abaffa/zx81/case_zx80/vacuum_mold2/48836-sinclair-zx80-vacuum-form-molds-40aaf106-83d1-470b-8c4a-8a237495e2ef.pdf

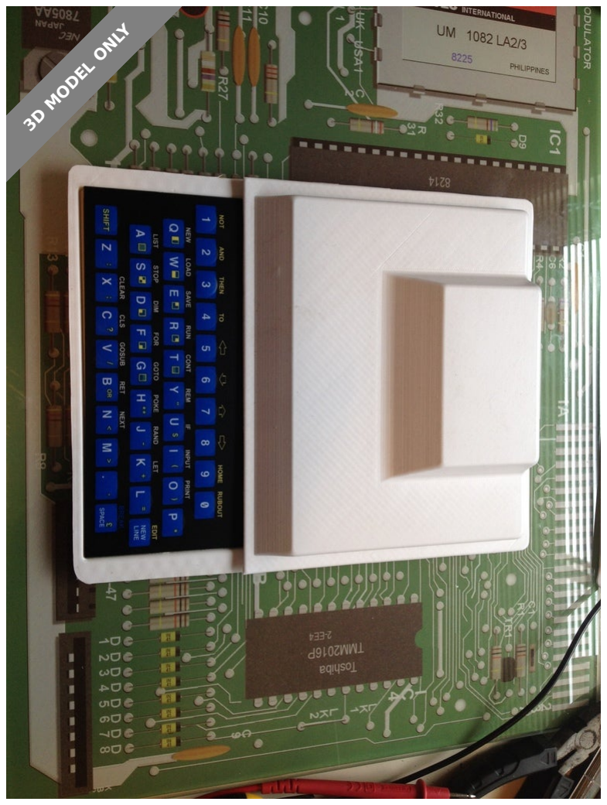
[picture p41: figure]
3D MODEL ONLY

## Summary

This is a first attempt at a vacuum form mold set for the Sinclair ZX80 computer. The ZX80's case was originally vacuum formed from polystyrene sheets, only later becoming injection molded.

This is an attempt to produce simple molds that can be made to replace the original cases which have become very brittle due to their age, or for a new ZX80 replica. The Sinclair ZX80 computer was produced by a company called "Science Of Cambridge" (Later renamed Sinclar Research) in 1980 and was powered by the Zilog Z80 Microprocessor and utilized 4k of Rom and 1k of Ram.

Hobby & Makers (https://www.prusaprinters.org/prints?categoryId=48) > Electronics (https://www.prusaprinters.org/prints?categoryId=52)

zx80 | sinclair | case

w (https://www.prusaprinters.org/social/27897/prints) wjsteele (https://www.prusaprinters.org/social/27897/prints)

## Sinclair ZX80 Vacuum Form Molds

VIEW IN BROWSER (https://www.prusaprinters.org/prints/48836-sinclair-zx80-vacuum-form-molds)

updated 14. 12. 2020 | published 14. 12. 2020

Model Files (.stl, .3mf, .obj, .amf) | F3 3D DOWNLOAD ALL FILES (https://www.prusaprinters.org/prints/48836-sinclair-zx80-vacuum-form-molds/files)

18.1 KB
updated 14. 12. 2020

F3
3D (https://www.prusaprinters.org/prints/48836-sinclair-zx80-vacuum-form-molds/files)

59.3 KB
updated 14. 12. 2020

F3
3D (https://www.prusaprinters.org/prints/48836-sinclair-zx80-vacuum-form-molds/files)

2.6 MB
updated 14. 12. 2020

F3
3D (https://www.prusaprinters.org/prints/48836-sinclair-zx80-vacuum-form-molds/files)

6.0 MB
updated 14. 12. 2020

F3
3D (https://www.prusaprinters.org/prints/48836-sinclair-zx80-vacuum-form-molds/files)

F3
0F

## Category: Computer Summary

This is a first attempt at a vacuum form mold set for the Sinclair ZX80 computer. The ZX80's case was originally vacuum formed from polystyrene sheets, only later becoming injection molded.

This is an attempt to produce simple molds that can be made to replace the original cases which have become very brittle due to their age, or for a new ZX80 replica. The Sinclair ZX80 computer was produced by a company called "Science Of Cambridge" (Later renamed Sinclar Research) in 1980 and was powered by the Zilog Z80 Microprocessor and utilized 4k of Rom and 1k of Ram.

Find source .stl files on Thingiverse.com (https://www.thingiverse.com/thing:2587664)

The Author has not uploaded any print files.
Try to search in User print files (https://www.prusaprinters.org/prints/48836-sinclair-zx80-vacuum-form-molds/user-gcodes) section or generate and upload your own.

zx80_top_mold.stl

zx80_top_mold.skp

zx80_bottom_mold.skp

zx80_bottom_mold.stl

## License

This work is licensed under a
Creative Commons (International License)

Public Domain (https://creativecommons.org/share-your-work/public-domain/cc0/)

✔ | Sharing without ATTRIBUTION
✔ | Remix Culture allowed
✔ | Commercial Use
✔ | Free Cultural Works
✔ | Meets Open Definition
