abaffa/zx81/keyboard/keyboard_acetate_separator.pdf

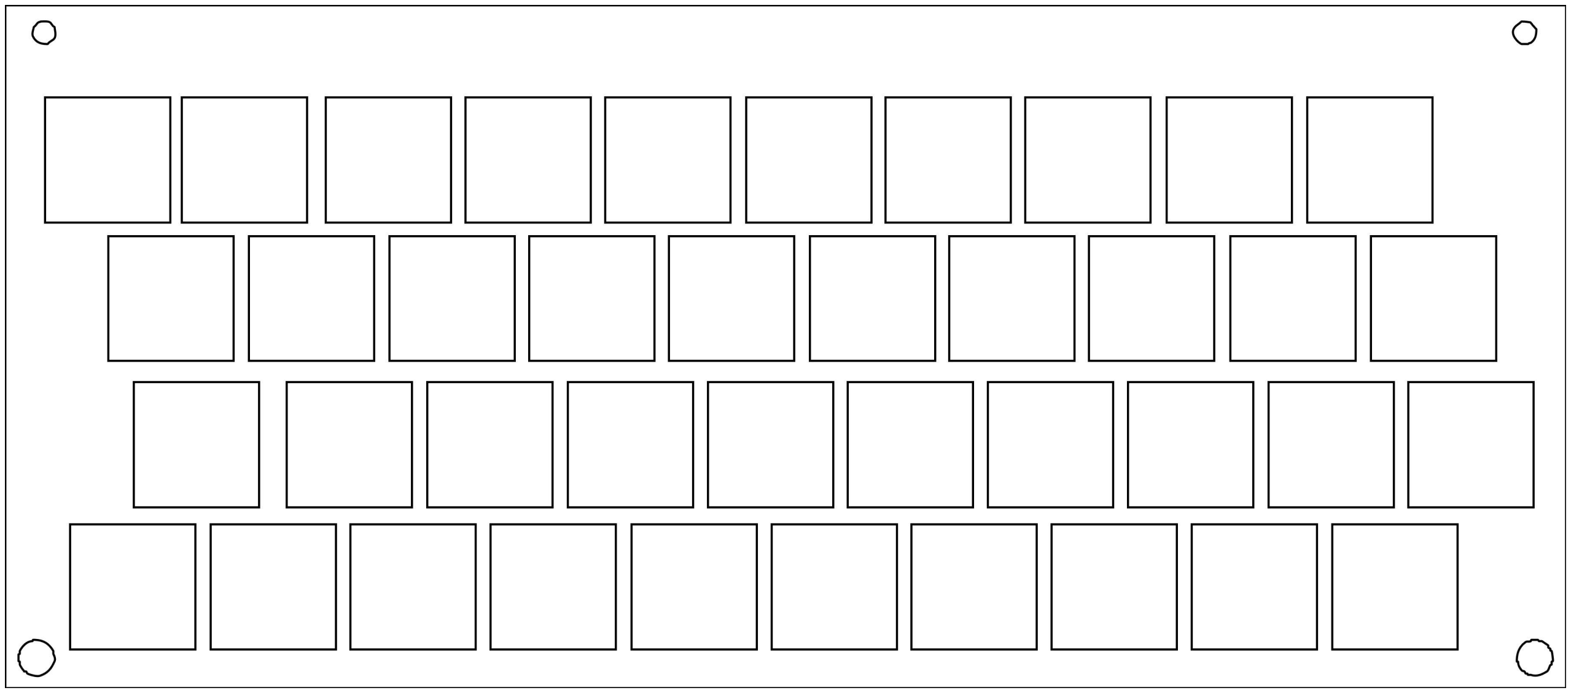
[picture p43: figure]
