abaffa/zx81/keyboard/keyboard_mask.pdf

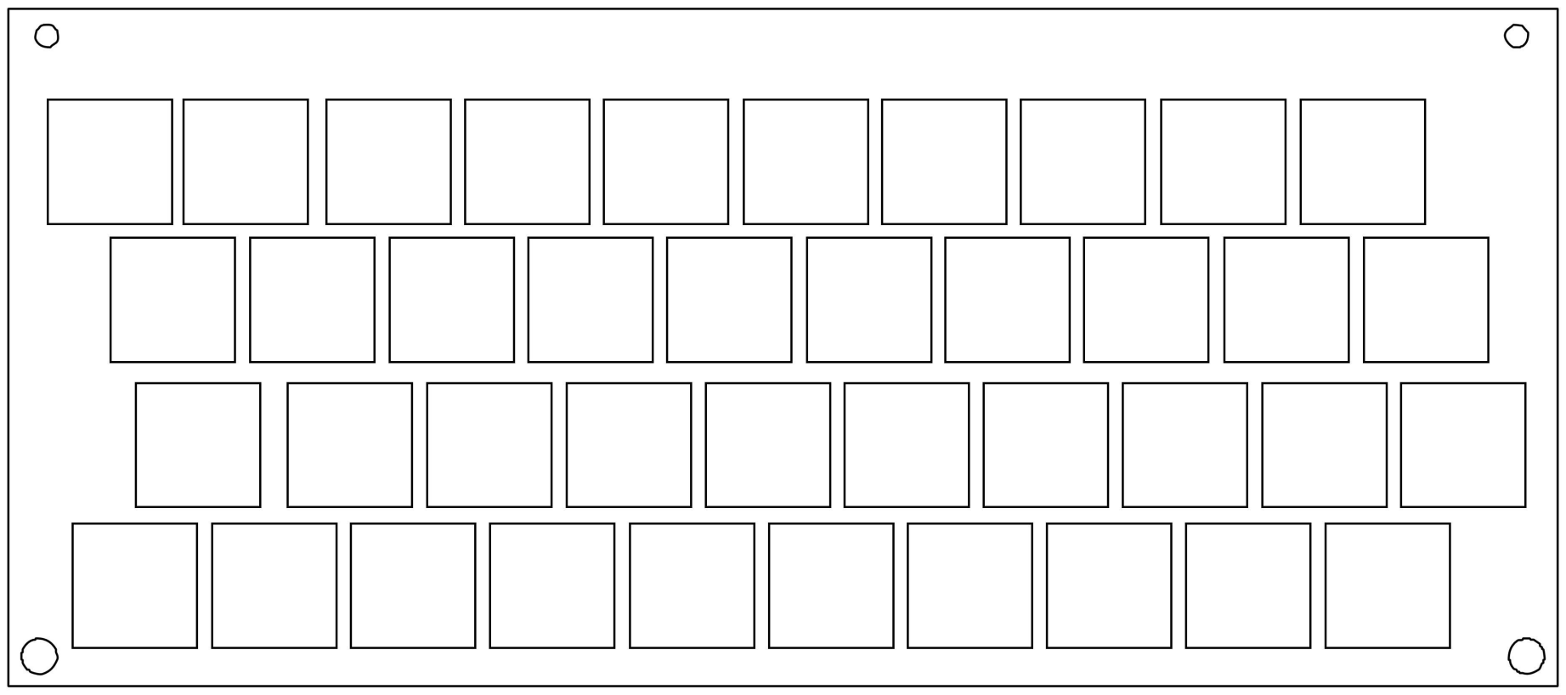
[picture p44: figure]
