abaffa/zx81/keyboard/keyboard_zx80_color.pdf

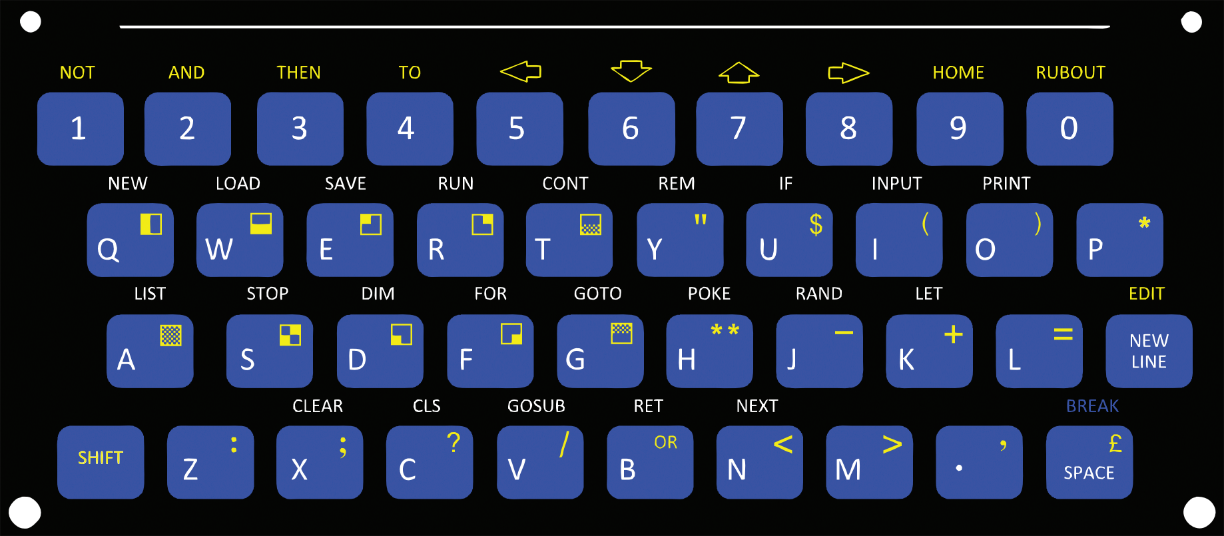
[picture p45: page 1]
