abaffa/zx81/keyboard/keyboard_zx80_pb_A4.pdf

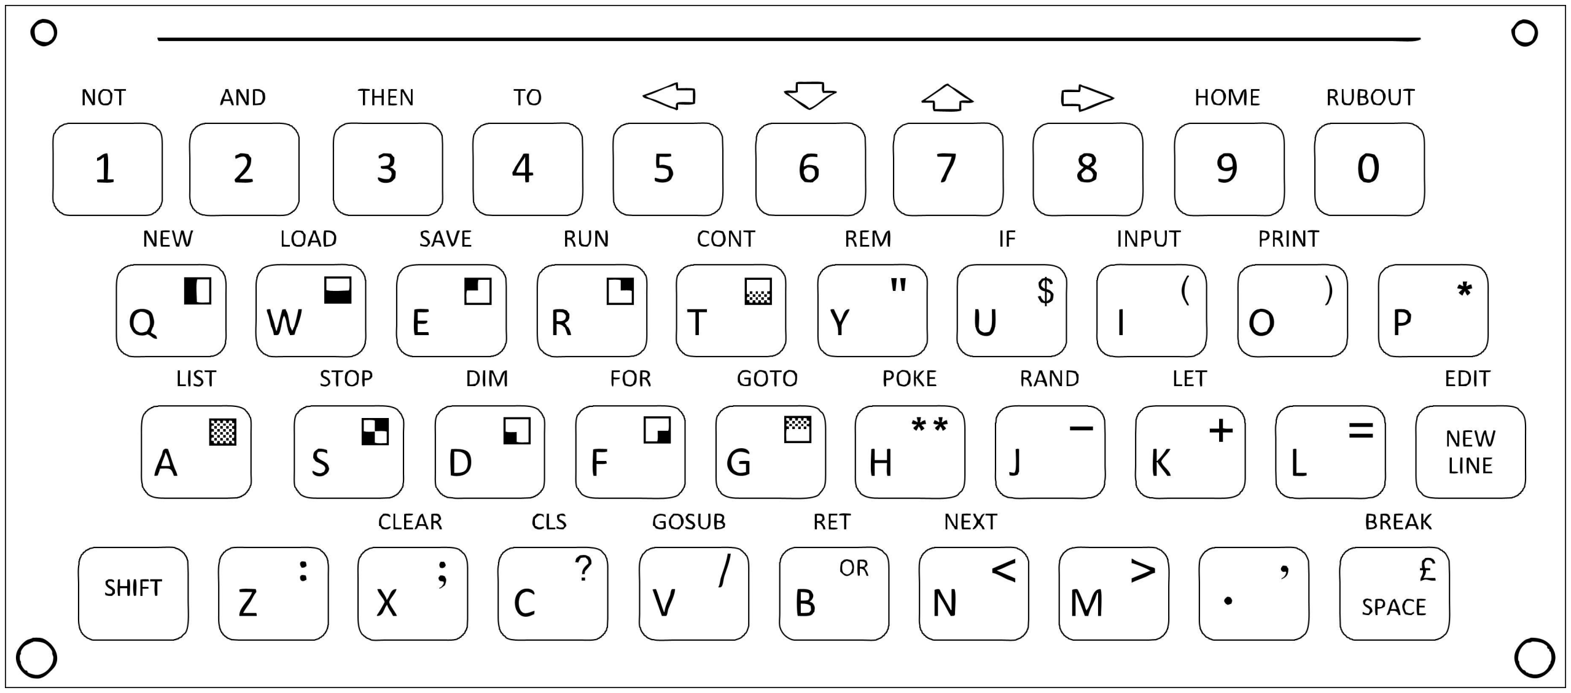
[picture p46: figure]
