abaffa/zx81/keyboard/keyboard_zx81_pb_A4.pdf

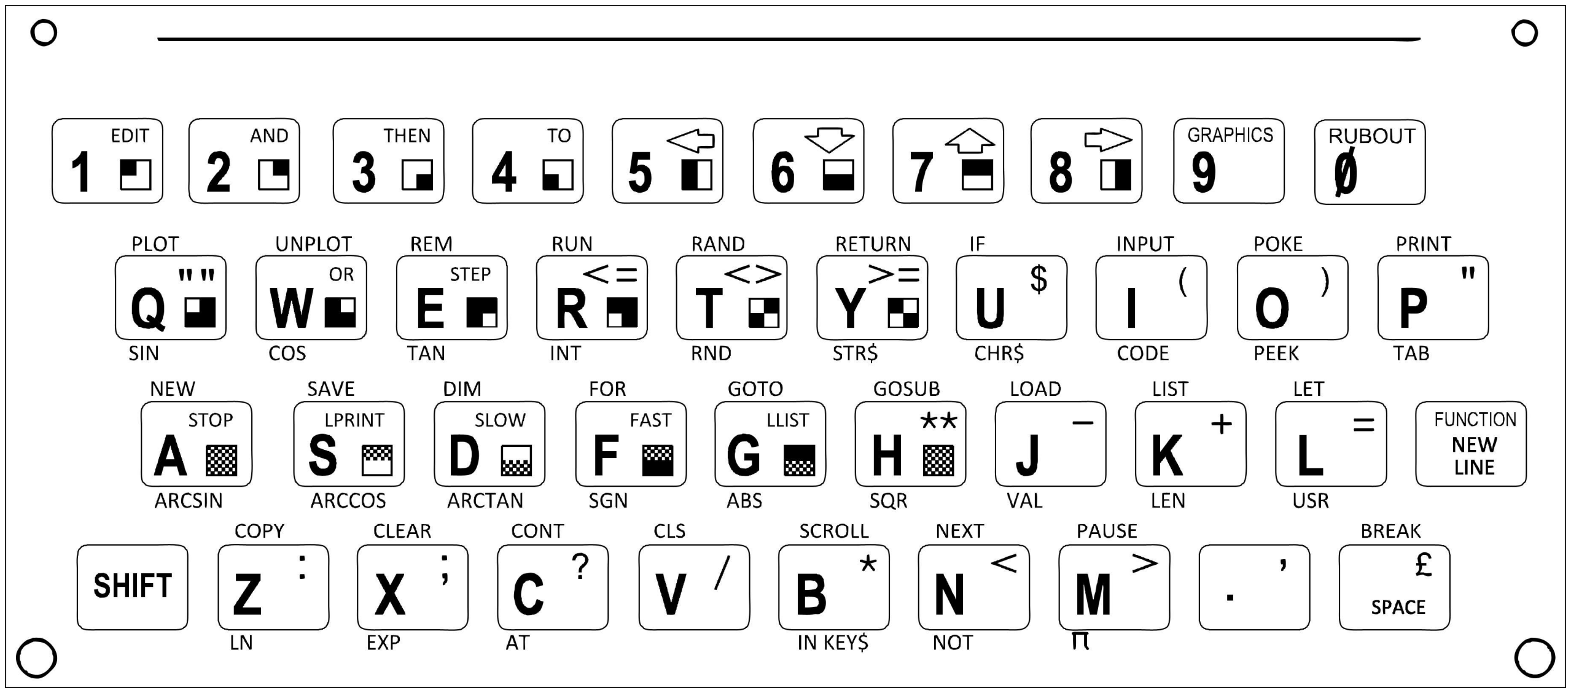
[picture p47: figure]
