abaffa/zx81/stickers/_sample_applied_stickers.pdf

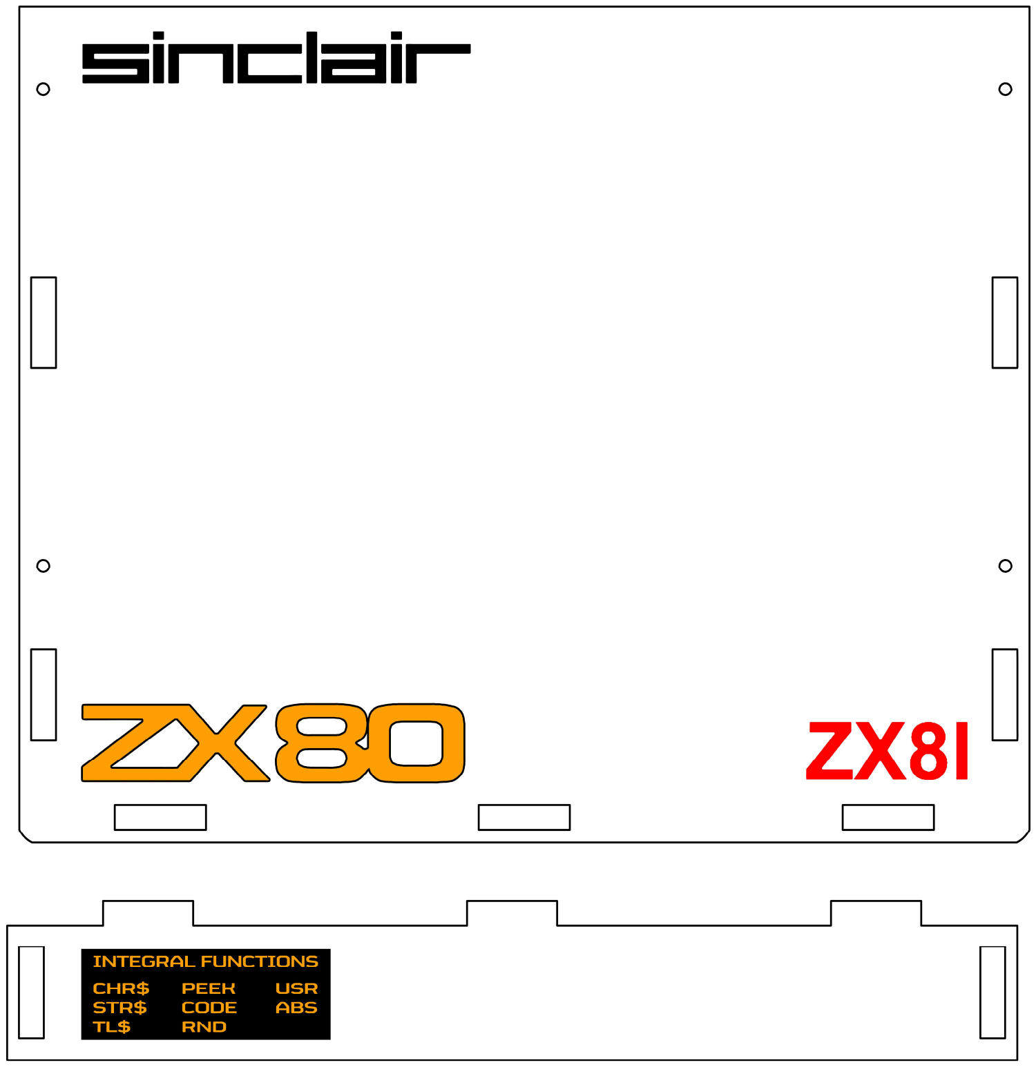
[picture p48: page 1]
