abaffa/zx81/stickers/Labels_ZX80.pdf

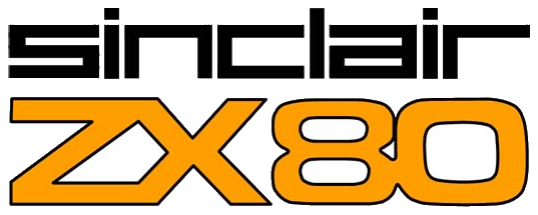
[picture p49: figure]
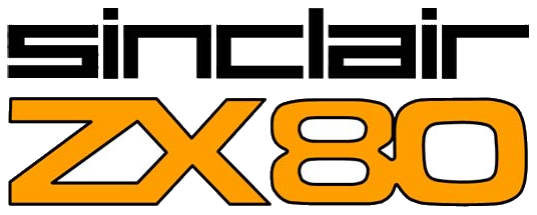
[picture p50: figure]
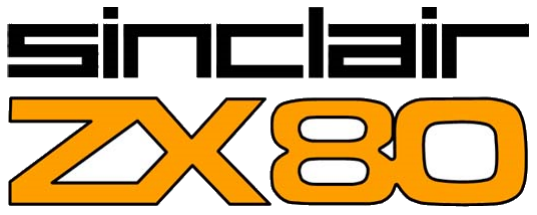
[picture p51: figure]
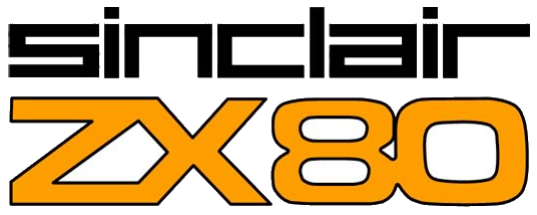
[picture p52: figure]
