abaffa/zx81/stickers/sticker_functions.pdf

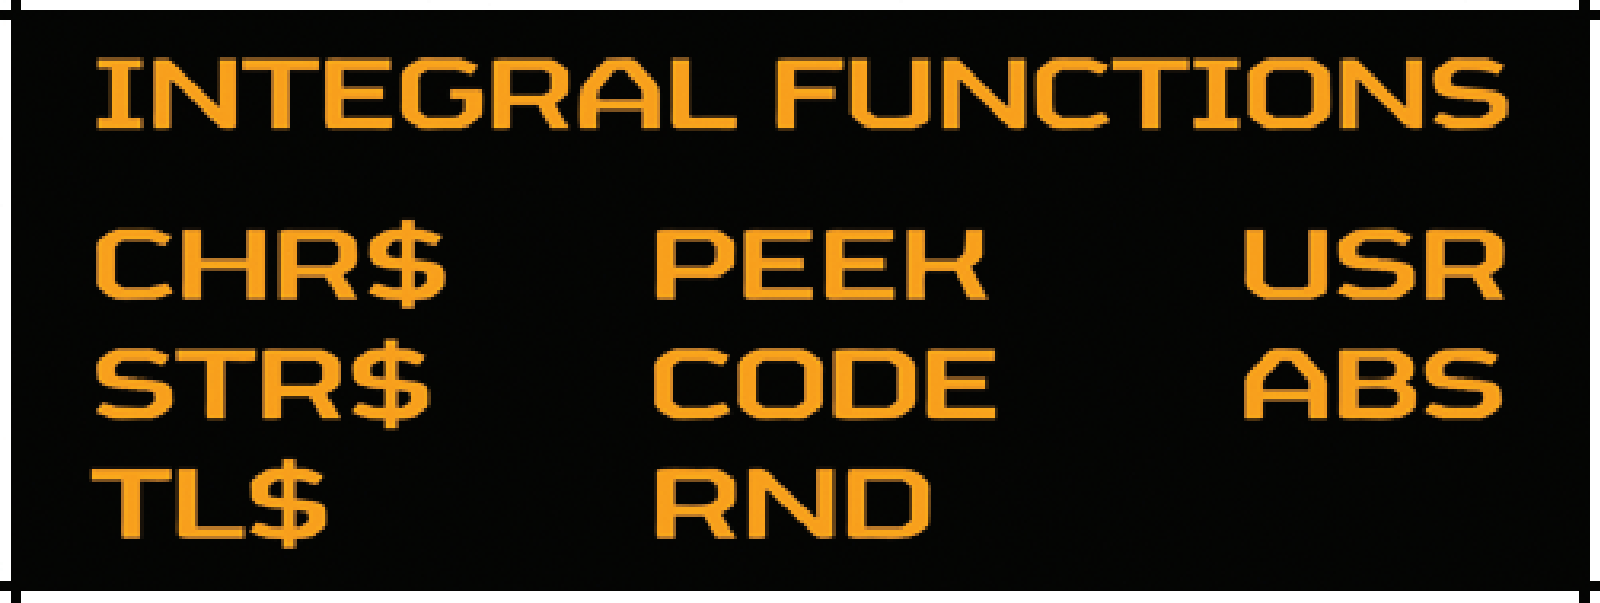
[picture p53: page 1]
