abaffa/zx81/stickers/sticker_zx80.pdf

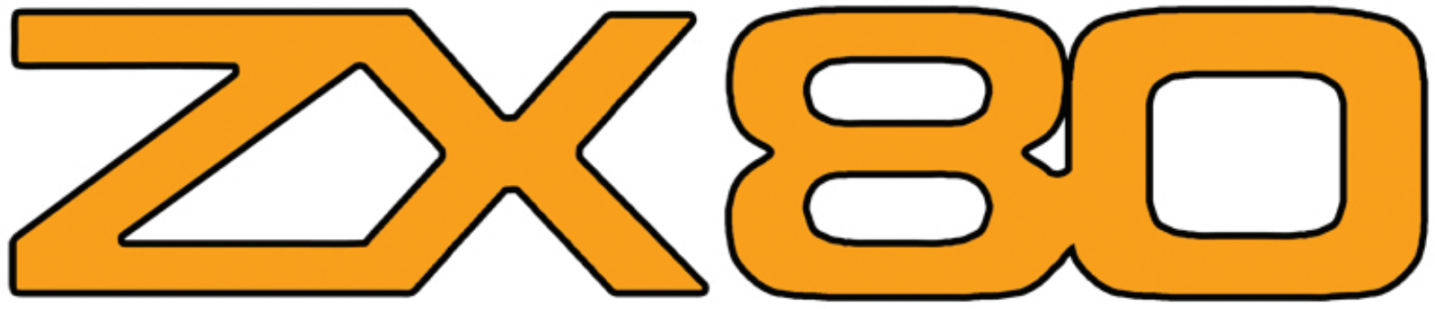
[picture p54: page 1]
