abaffa/zx81/stickers/stickers_A4.pdf

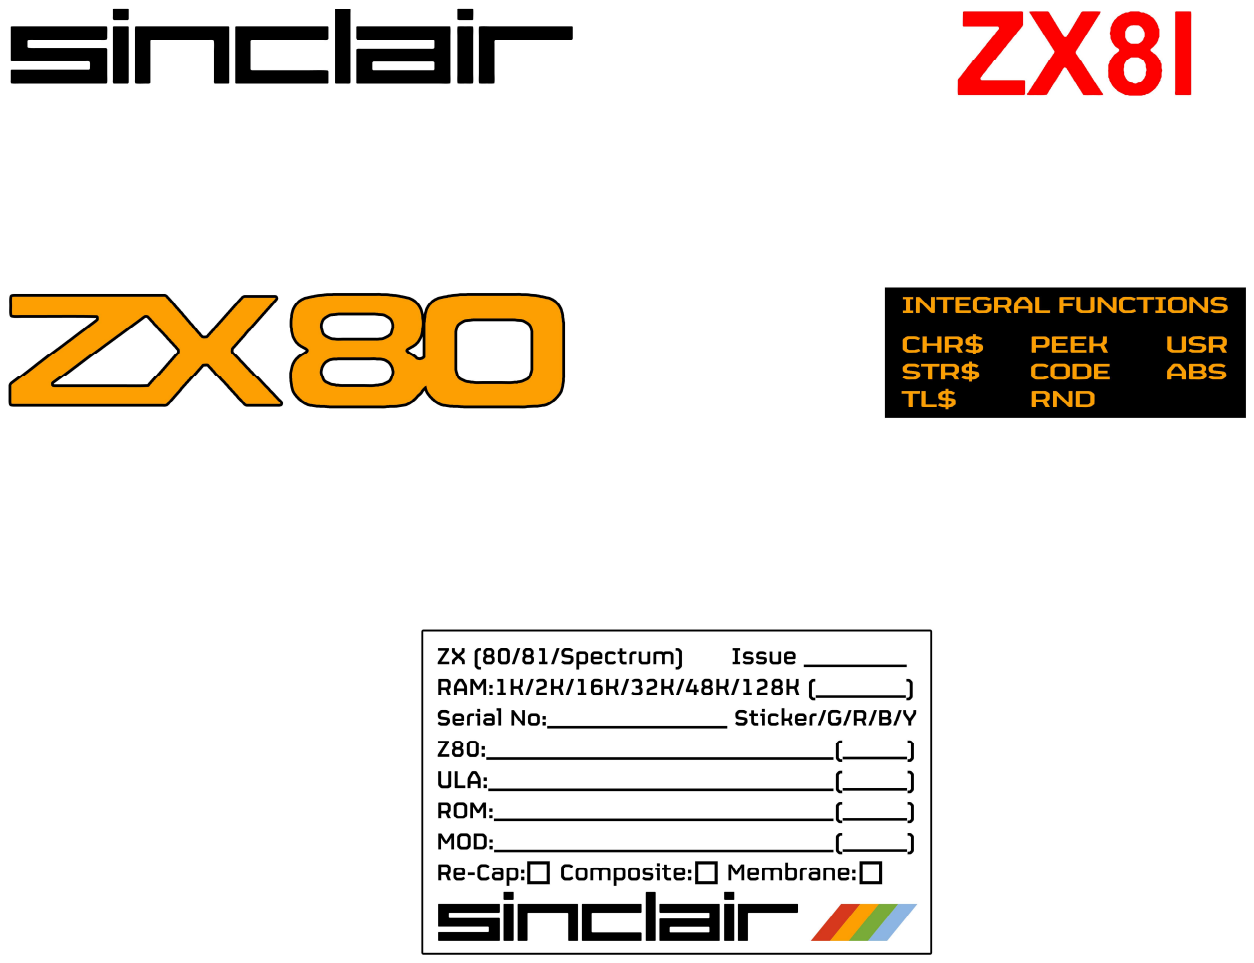
[picture p55: page 1]
