abaffa/zx81/project/board_drill_mask.pdf

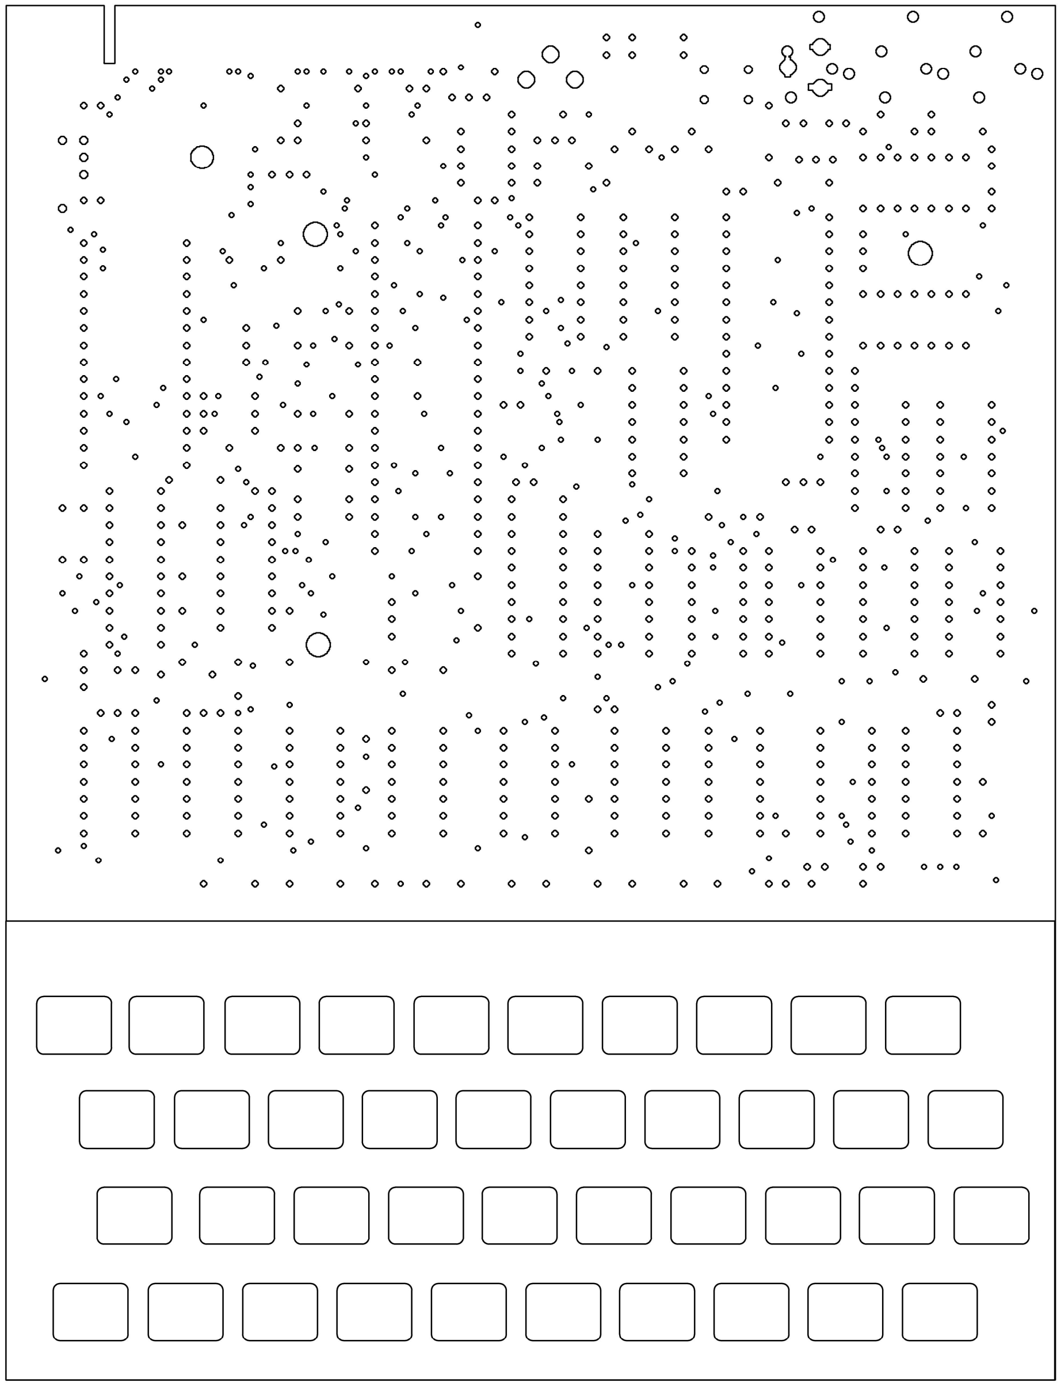
[picture p56: figure]
