abaffa/zx81/_zx81/_images/expansion 2.jpg

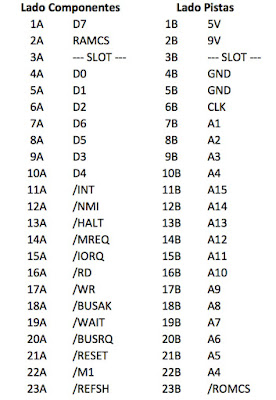
_zx81/_images/expansion 2.jpg
