abaffa/zx81/_zx81/_images/expansion 3.jpg

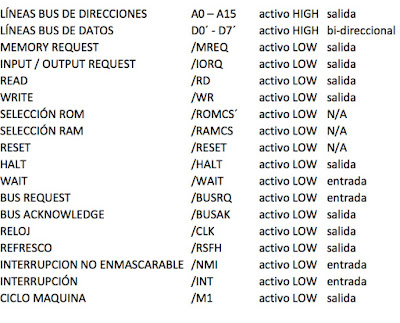
_zx81/_images/expansion 3.jpg
