abaffa/zx81/_zx81/peripherals/32k-newdecoder.gif

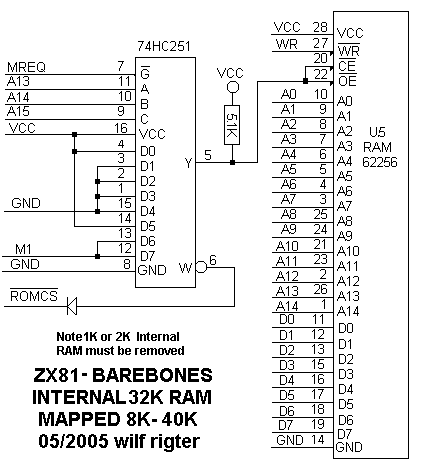
_zx81/peripherals/32k-newdecoder.gif
