abaffa/zx81/_zx81/peripherals/64k-newdecoder.gif

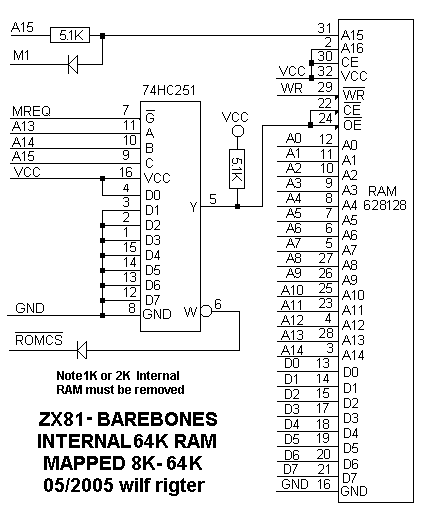
_zx81/peripherals/64k-newdecoder.gif
