abaffa/zx81/_zx81/peripherals/NEZ-8000_slowb.jpg

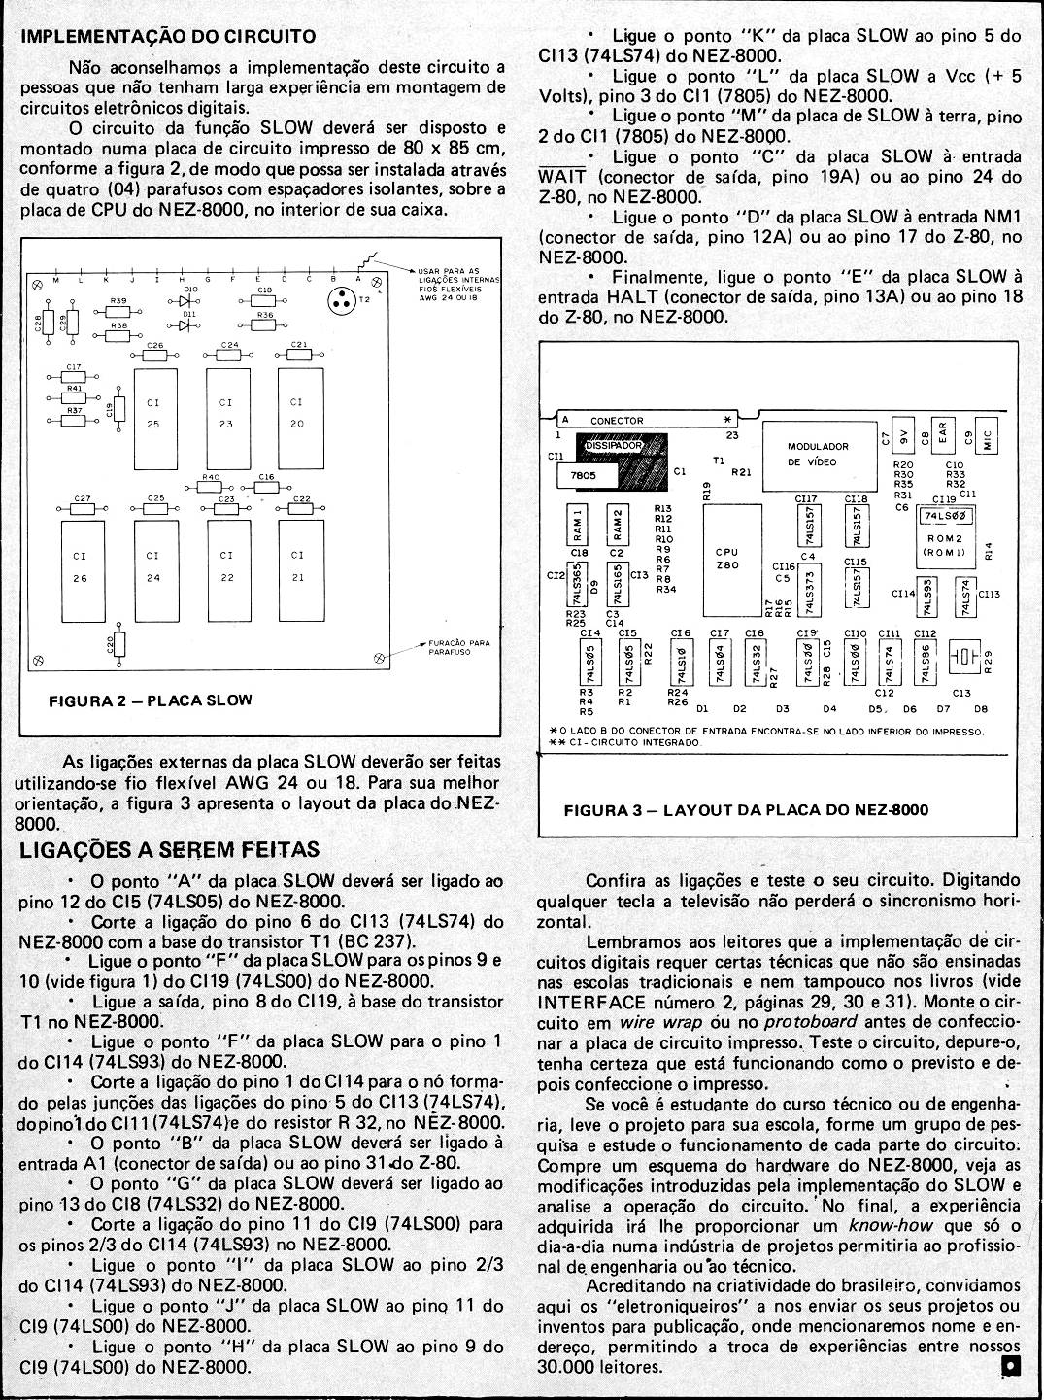
_zx81/peripherals/NEZ-8000_slowb.jpg
