abaffa/zx81/_zx81/peripherals/ZX80_Edge_Connector_Diagram.jpg

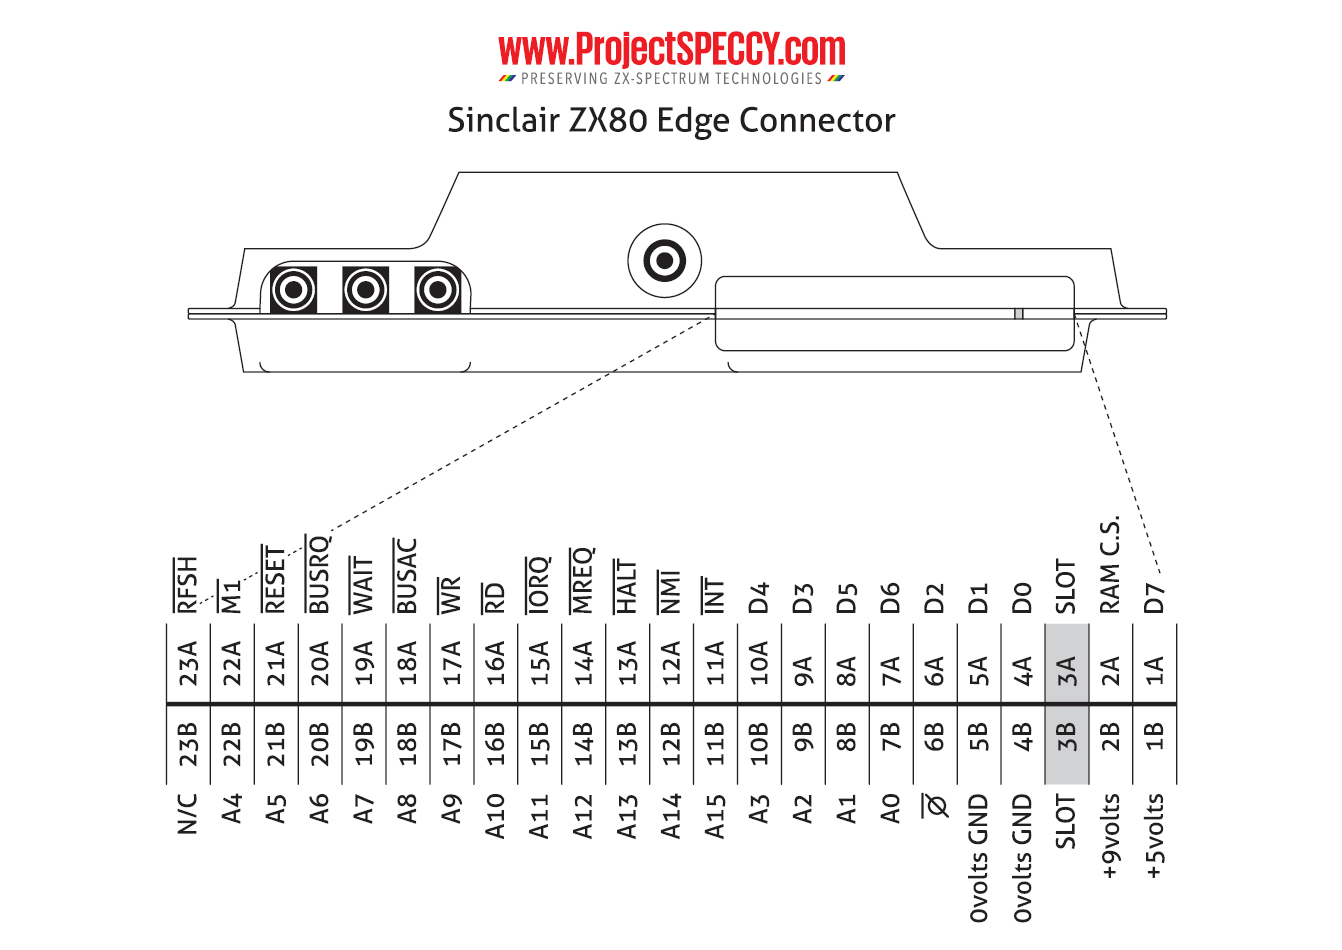
_zx81/peripherals/ZX80_Edge_Connector_Diagram.jpg
