abaffa/zx81/_zx81/peripherals/ZX81_Edge_Connector_Diagram.jpg

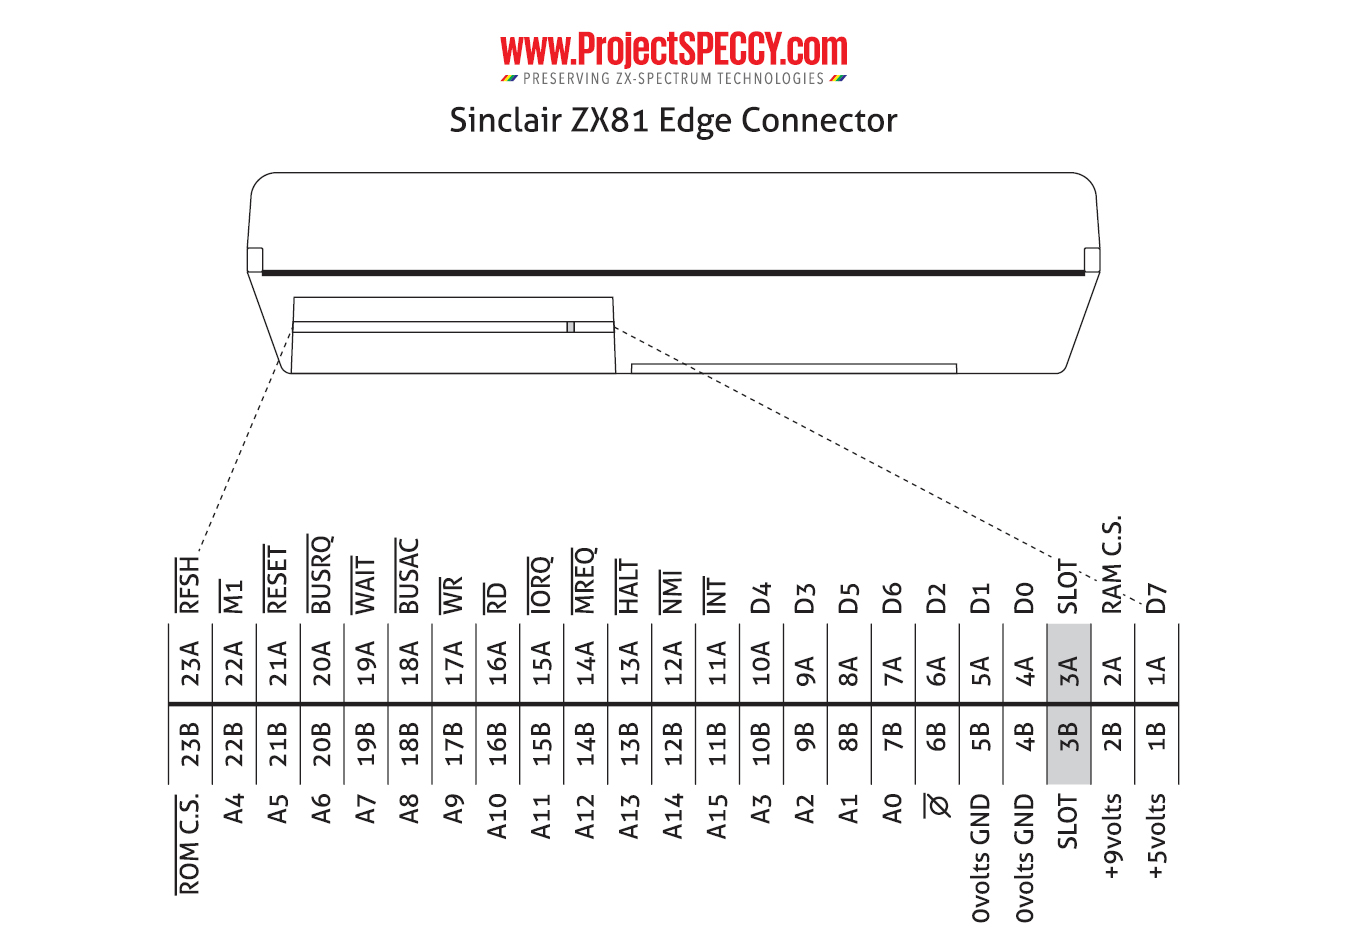
_zx81/peripherals/ZX81_Edge_Connector_Diagram.jpg
