abaffa/zx81/case_zx80/case1/images/2ab542ab22c95c155e1d55bb198a6562_preview_featured.jpg

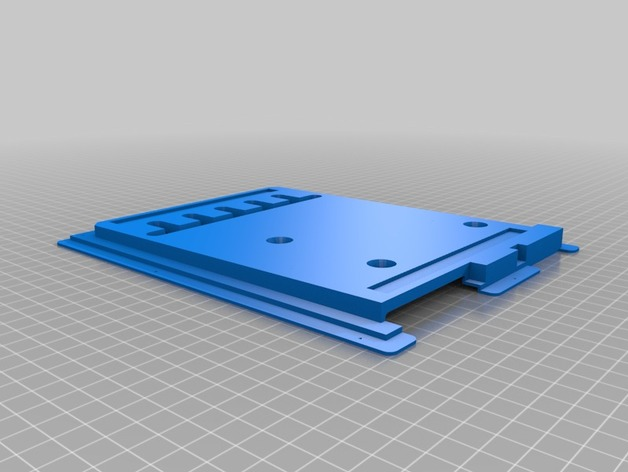
case_zx80/case1/images/2ab542ab22c95c155e1d55bb198a6562_preview_featured.jpg
