abaffa/zx81/case_zx80/case1/images/5d3d6aa979861b2aaec65e975a5817c5_preview_featured.jpg

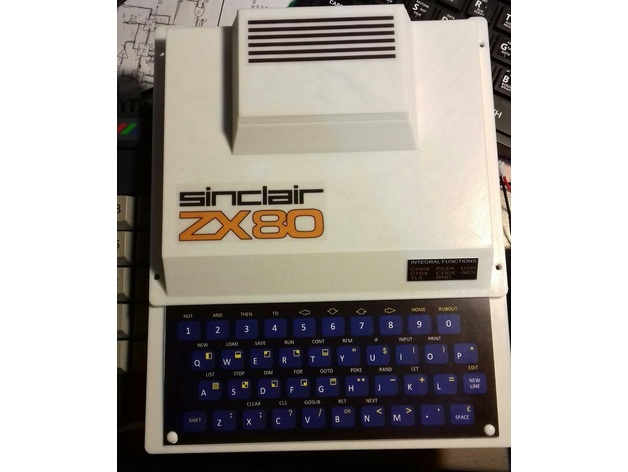
case_zx80/case1/images/5d3d6aa979861b2aaec65e975a5817c5_preview_featured.jpg
