abaffa/zx81/case_zx80/case1/images/7c27a81579bcb7c29772837ceefd6dca_preview_featured.jpg

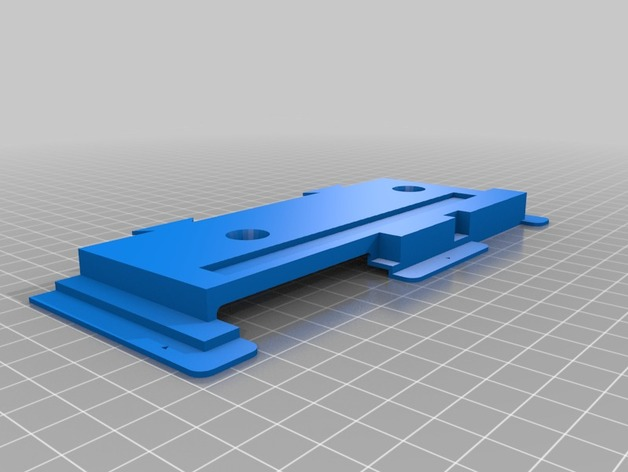
case_zx80/case1/images/7c27a81579bcb7c29772837ceefd6dca_preview_featured.jpg
