abaffa/zx81/case_zx80/case1/images/9c5d98d490175c6c0b64dd7ffe1bead8_preview_featured.jpg

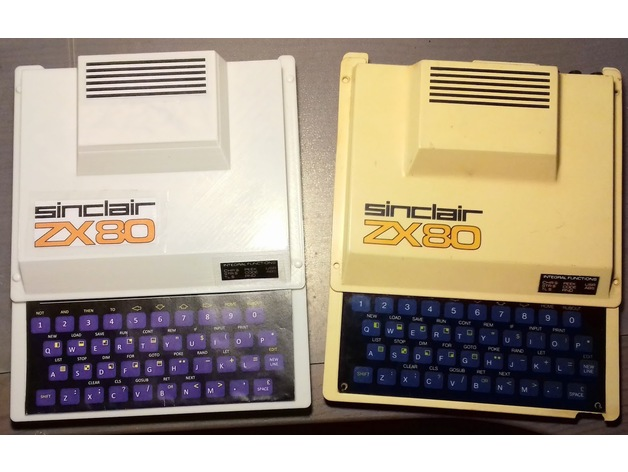
case_zx80/case1/images/9c5d98d490175c6c0b64dd7ffe1bead8_preview_featured.jpg
