abaffa/zx81/case_zx80/case1/images/14f81254bac9f5b3111d519f46a25c52_preview_featured.jpg

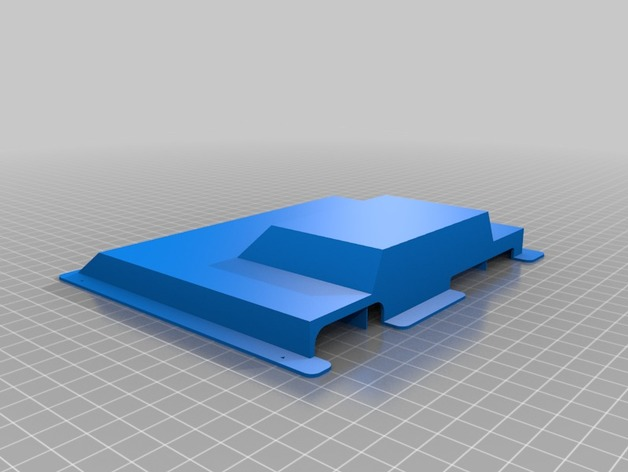
case_zx80/case1/images/14f81254bac9f5b3111d519f46a25c52_preview_featured.jpg
