abaffa/zx81/case_zx80/case1/images/2062f9475eb2afe823c7426697d6c0df_preview_featured.jpg

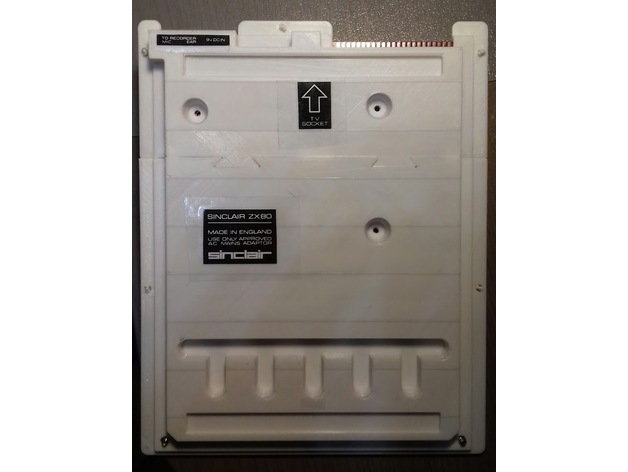
case_zx80/case1/images/2062f9475eb2afe823c7426697d6c0df_preview_featured.jpg
