abaffa/zx81/case_zx80/case1/images/cf2dca7d4f363c3d4e55715a756fce0d_preview_featured.jpg

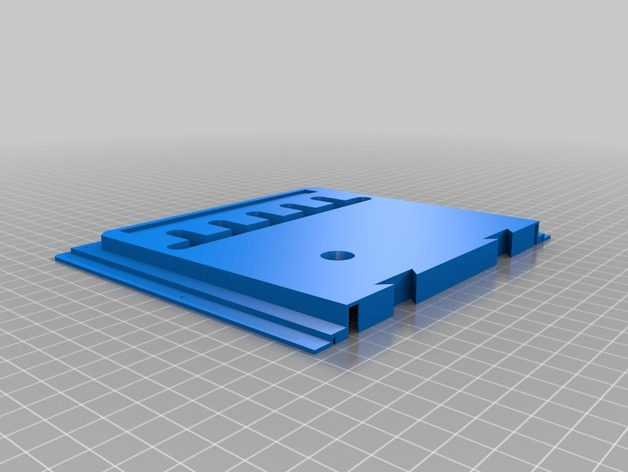
case_zx80/case1/images/cf2dca7d4f363c3d4e55715a756fce0d_preview_featured.jpg
