abaffa/zx81/case_zx80/case3/images/Bottom_join.jpg

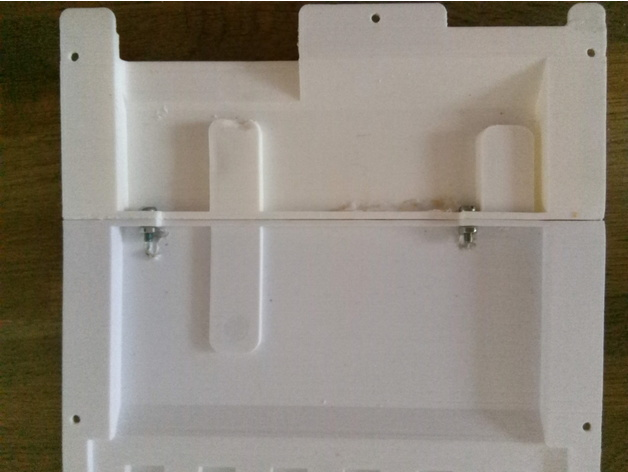
case_zx80/case3/images/Bottom_join.jpg
