abaffa/zx81/case_zx80/case3/images/Bottom_sections_Collage.jpg

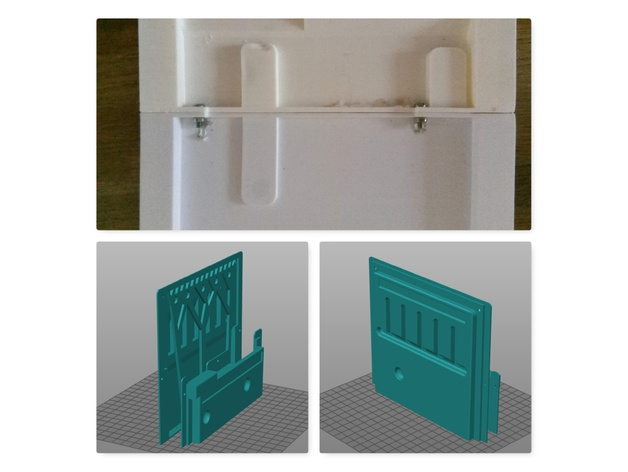
case_zx80/case3/images/Bottom_sections_Collage.jpg
