abaffa/zx81/case_zx80/case3/images/IMG_20200329_144656.jpg

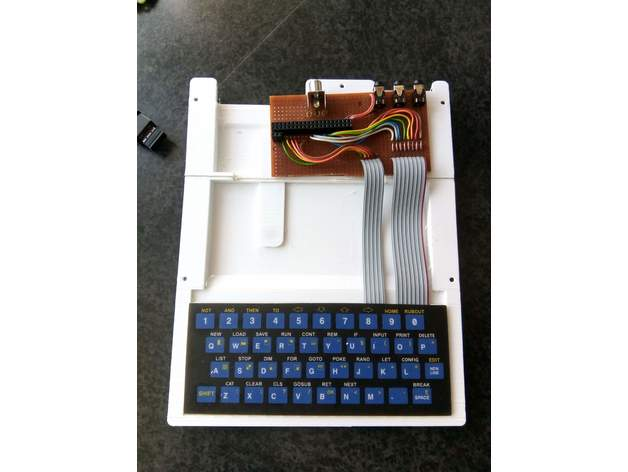
case_zx80/case3/images/IMG_20200329_144656.jpg
