abaffa/zx81/case_zx80/case3/images/IMG_20200330_174505.jpg

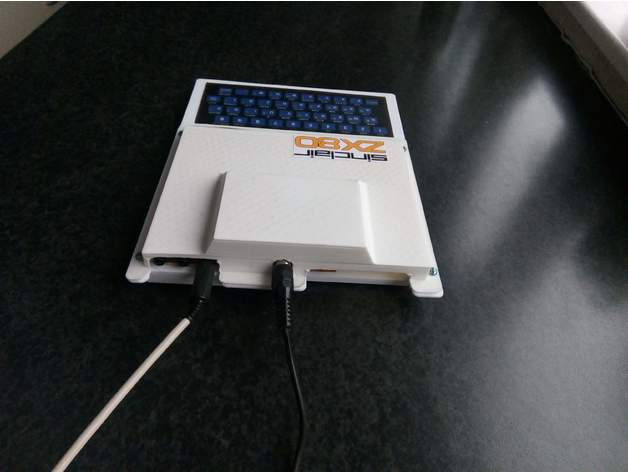
case_zx80/case3/images/IMG_20200330_174505.jpg
