abaffa/zx81/case_zx80/case3/images/ZX80_Final.png

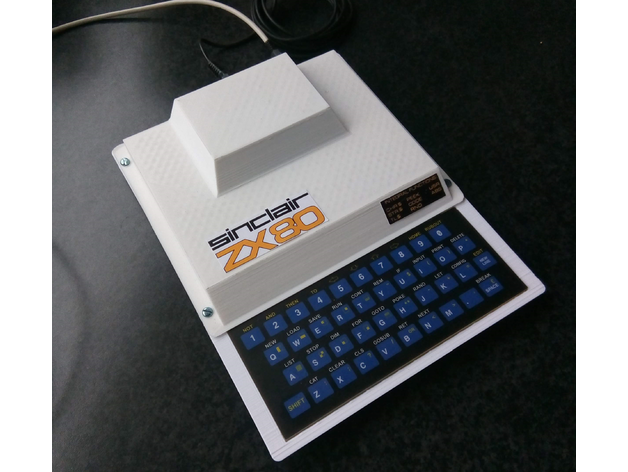
case_zx80/case3/images/ZX80_Final.png
