abaffa/zx81/case_zx80/case3/images/ZX-80_bottom_part1.png

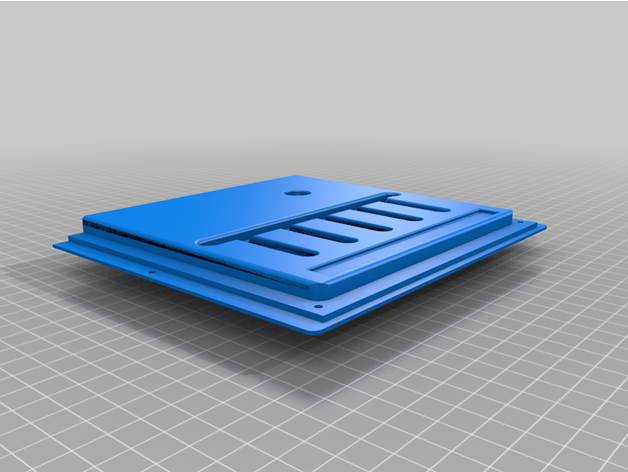
case_zx80/case3/images/ZX-80_bottom_part1.png
