abaffa/zx81/case_zx80/case3/images/ZX-80_top.png

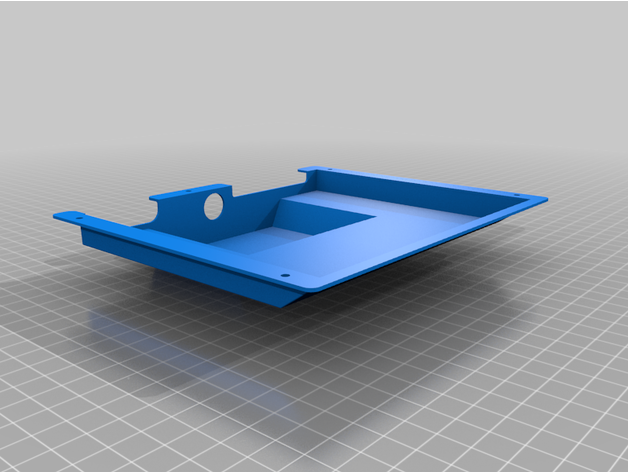
case_zx80/case3/images/ZX-80_top.png
