abaffa/zx81/case_zx80/vacuum_mold1/images/2e1f0ef28ea472878531f6873265fe98_preview_featured.jpg

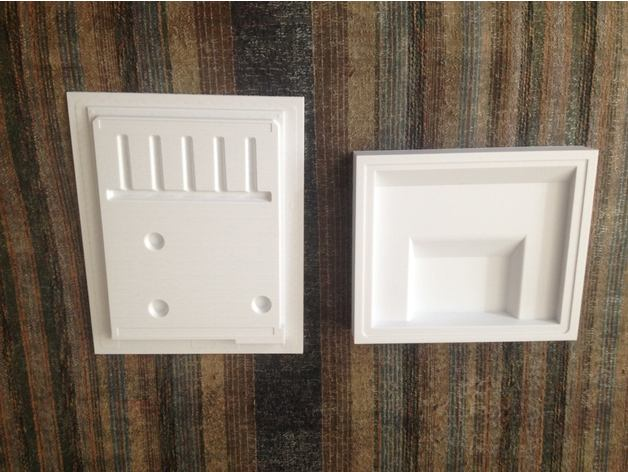
case_zx80/vacuum_mold1/images/2e1f0ef28ea472878531f6873265fe98_preview_featured.jpg
