abaffa/zx81/case_zx80/vacuum_mold1/images/40f460744047b8389b473ba0da1bde4e_preview_featured.JPG

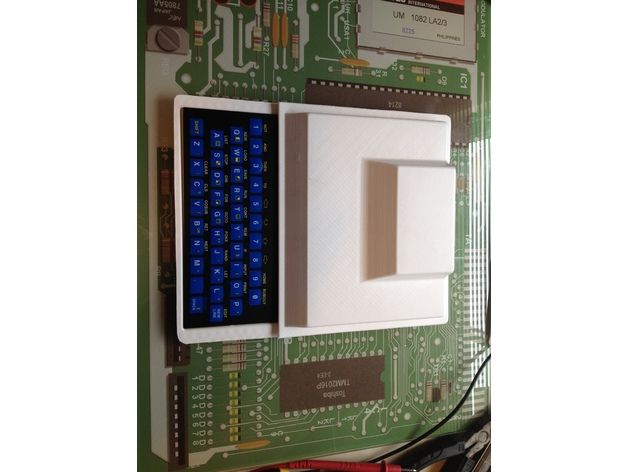
case_zx80/vacuum_mold1/images/40f460744047b8389b473ba0da1bde4e_preview_featured.JPG
