abaffa/zx81/case_zx80/vacuum_mold1/images/45a4155d389e4115a1ef50e9a0f32562_preview_featured.jpg

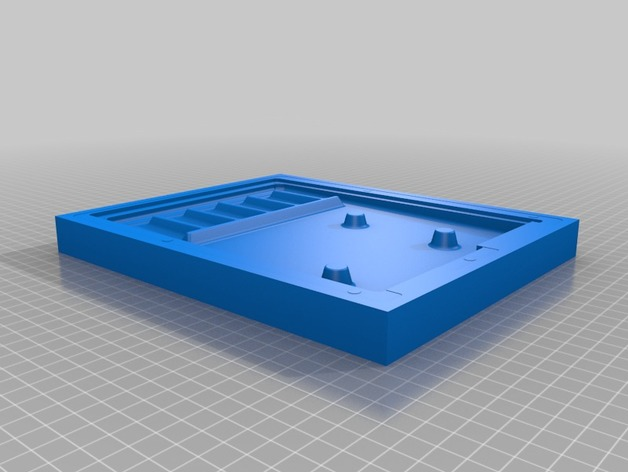
case_zx80/vacuum_mold1/images/45a4155d389e4115a1ef50e9a0f32562_preview_featured.jpg
