abaffa/zx81/case_zx80/vacuum_mold1/images/97af66a171a14e67437aeb69982622e7_preview_featured.JPG

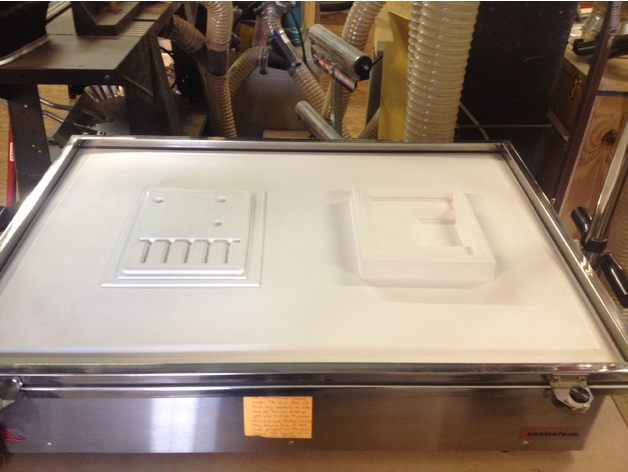
case_zx80/vacuum_mold1/images/97af66a171a14e67437aeb69982622e7_preview_featured.JPG
