abaffa/zx81/case_zx80/vacuum_mold1/images/7354ab5904b53d0a861096a2bb55e1ff_preview_featured.JPG

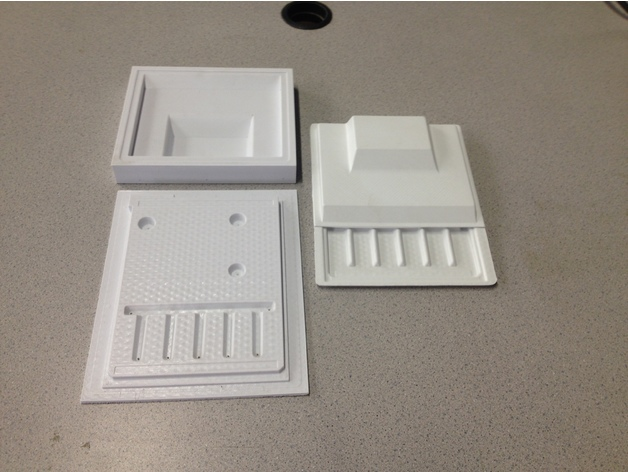
case_zx80/vacuum_mold1/images/7354ab5904b53d0a861096a2bb55e1ff_preview_featured.JPG
