abaffa/zx81/case_zx80/vacuum_mold1/images/08032439e0fef06d90d83156f67b39be_preview_featured.JPG

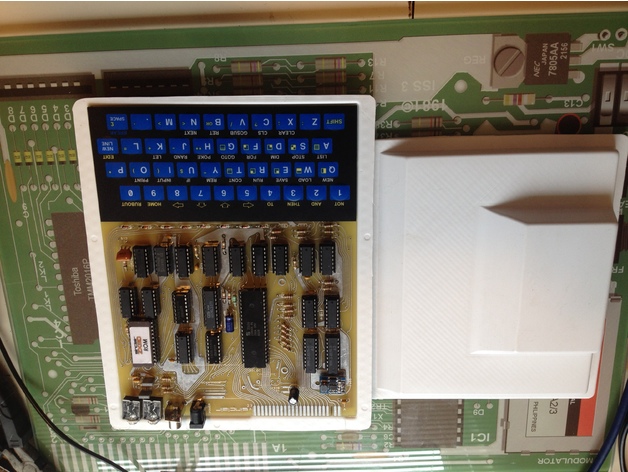
case_zx80/vacuum_mold1/images/08032439e0fef06d90d83156f67b39be_preview_featured.JPG
