abaffa/zx81/case_zx80/vacuum_mold1/images/a68eb5e813dc57dc1e89385d4ba02790_preview_featured.jpg

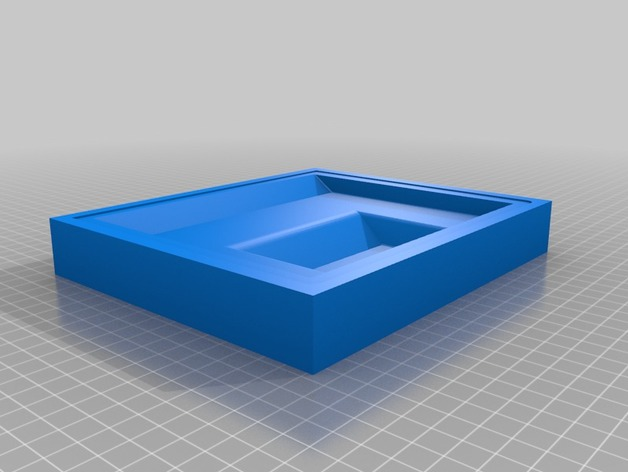
case_zx80/vacuum_mold1/images/a68eb5e813dc57dc1e89385d4ba02790_preview_featured.jpg
