abaffa/zx81/case_zx80/vacuum_mold1/images/aee9ccaca266b5cf5915d4f036aabd59_preview_featured.JPG

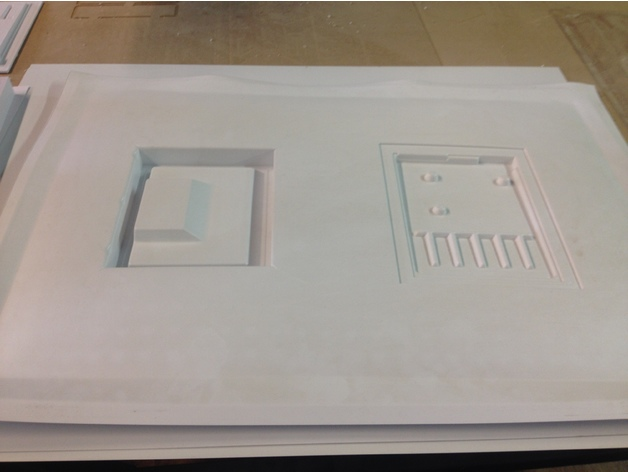
case_zx80/vacuum_mold1/images/aee9ccaca266b5cf5915d4f036aabd59_preview_featured.JPG
