abaffa/zx81/case_zx81/case1/images/ZX81-1.JPG

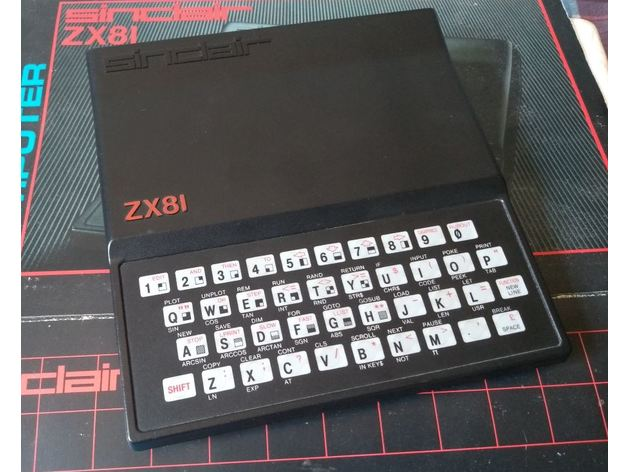
case_zx81/case1/images/ZX81-1.JPG
