abaffa/zx81/case_zx81/case1/images/ZX81-2.JPG

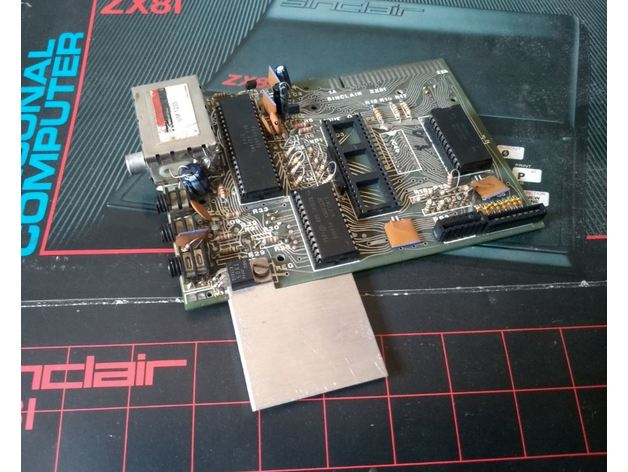
case_zx81/case1/images/ZX81-2.JPG
