abaffa/zx81/case_zx81/case1/images/ZX81-3.JPG

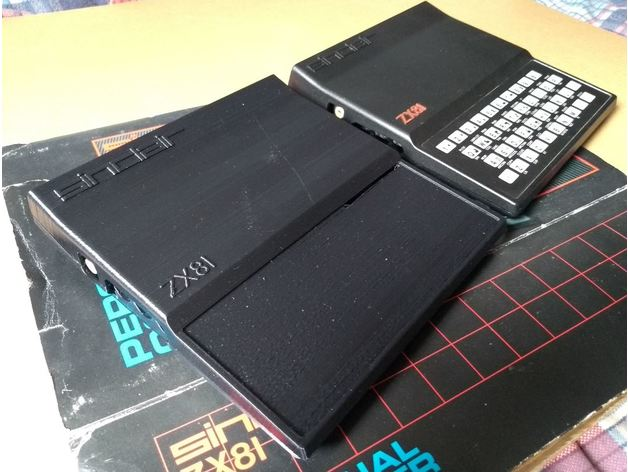
case_zx81/case1/images/ZX81-3.JPG
