abaffa/zx81/case_zx81/case1/images/zx81_case_bottom.png

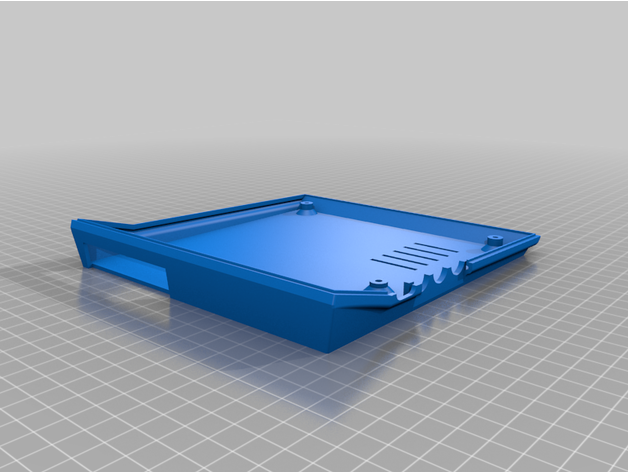
case_zx81/case1/images/zx81_case_bottom.png
