abaffa/zx81/case_zx81/case1/images/zx81_case_top-vertical.png

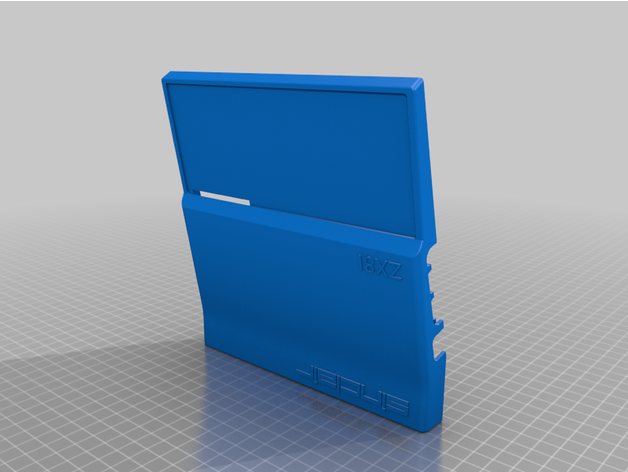
case_zx81/case1/images/zx81_case_top-vertical.png
