abaffa/zx81/case_zx81/case1/images/zx81_case_top.png

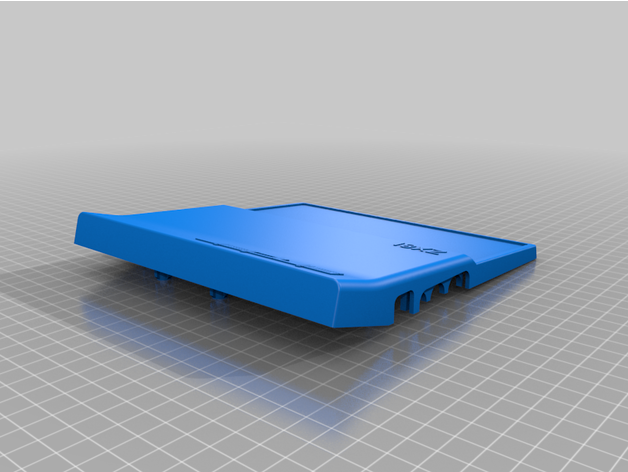
case_zx81/case1/images/zx81_case_top.png
