abaffa/zx81/case_zx81/case2/images/zx81-case-bottom.png

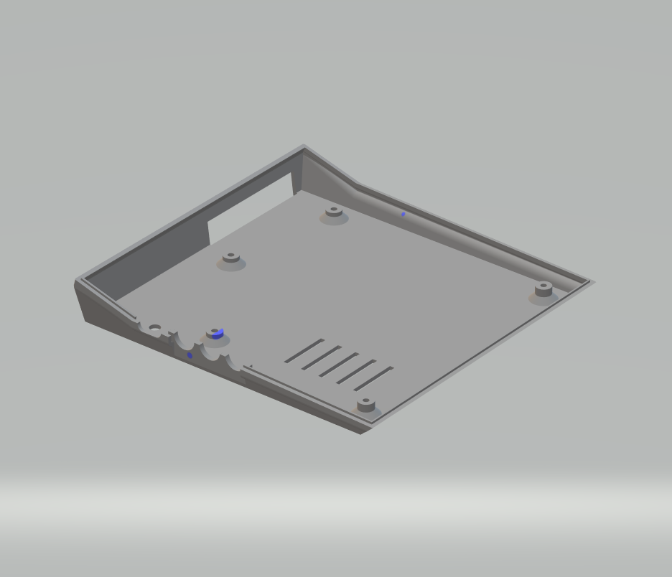
case_zx81/case2/images/zx81-case-bottom.png
