abaffa/zx81/case_zx81/case2/images/zx81-case-top-vertical-with-standoff-ribs.png

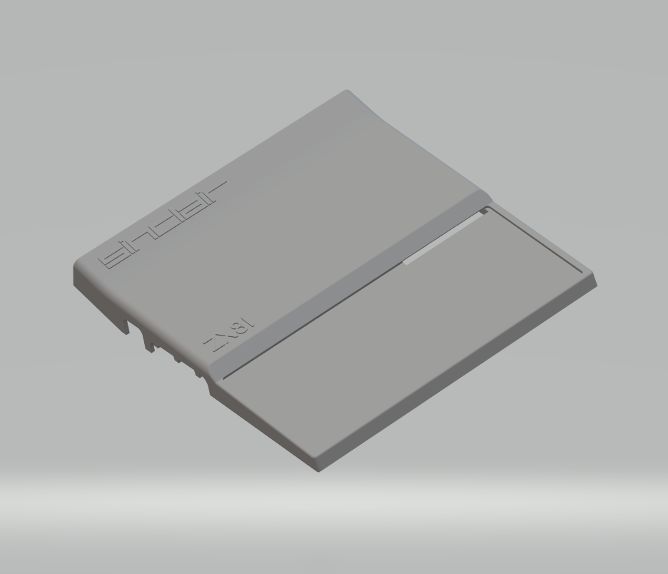
case_zx81/case2/images/zx81-case-top-vertical-with-standoff-ribs.png
