abaffa/zx81/case_zx81/case2/images/zx81-foot.png

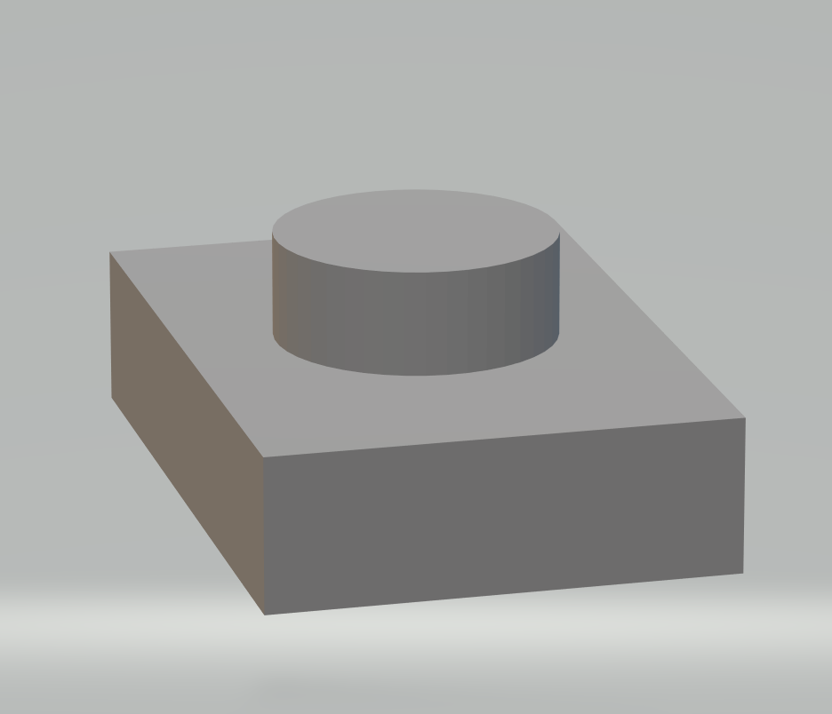
case_zx81/case2/images/zx81-foot.png
