abaffa/zx81/case_zx81/case3/images/zx81Block.png

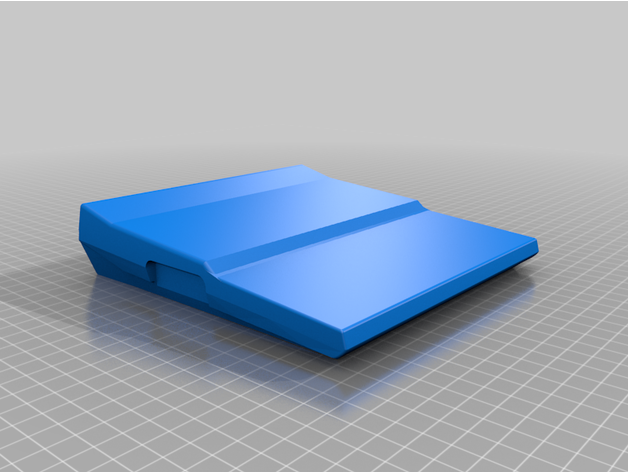
case_zx81/case3/images/zx81Block.png
