abaffa/zx81/case_zx81/case3/images/zx81Bottom-EuroPort.png

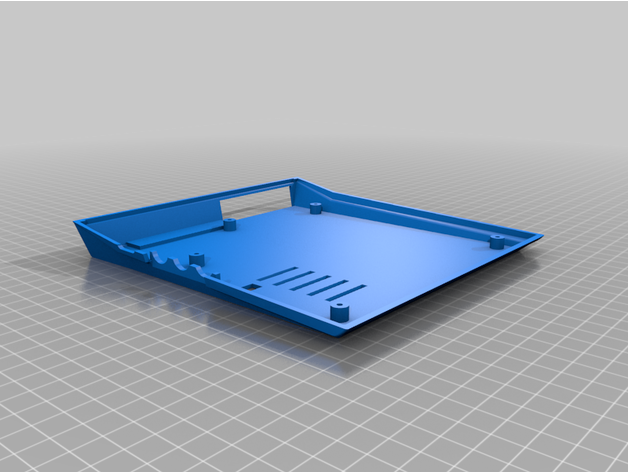
case_zx81/case3/images/zx81Bottom-EuroPort.png
