abaffa/zx81/case_zxspectrum/images/render2_preview_featured.jpg

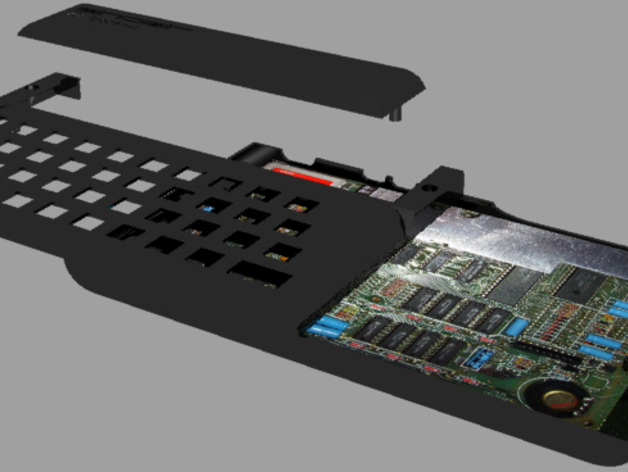
case_zxspectrum/images/render2_preview_featured.jpg
