abaffa/zx81/case_zxspectrum/images/render3_preview_featured.jpg

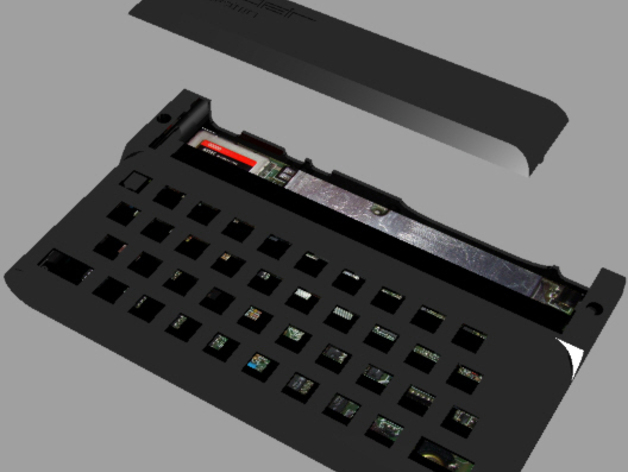
case_zxspectrum/images/render3_preview_featured.jpg
