abaffa/zx81/case_zxspectrum/images/render_preview_featured.jpg

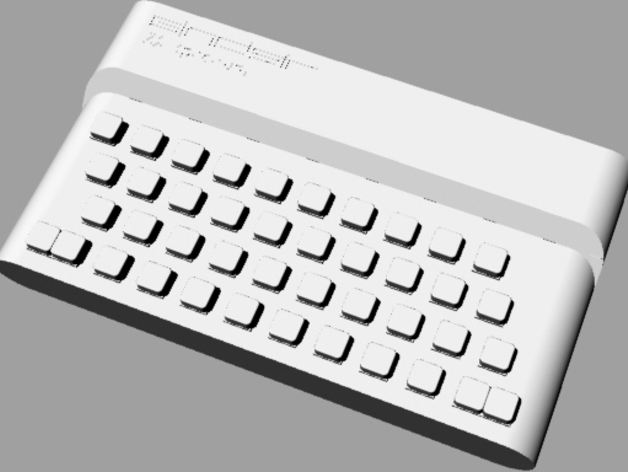
case_zxspectrum/images/render_preview_featured.jpg
