abaffa/zx81/case_zxspectrum/images/Rhino_preview_featured.jpg

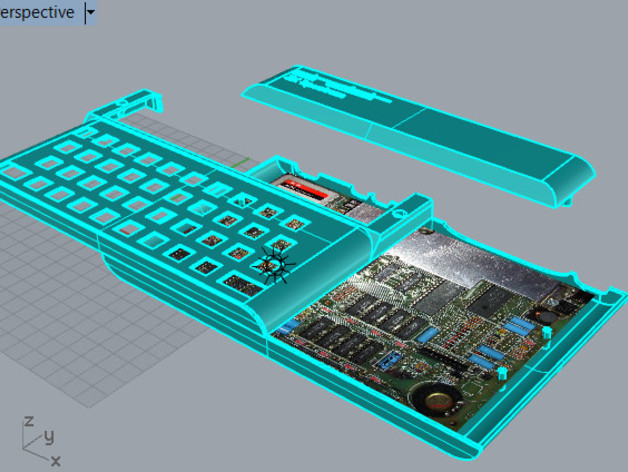
case_zxspectrum/images/Rhino_preview_featured.jpg
