abaffa/zx81/keyboard/keyboard_zx81_color.png

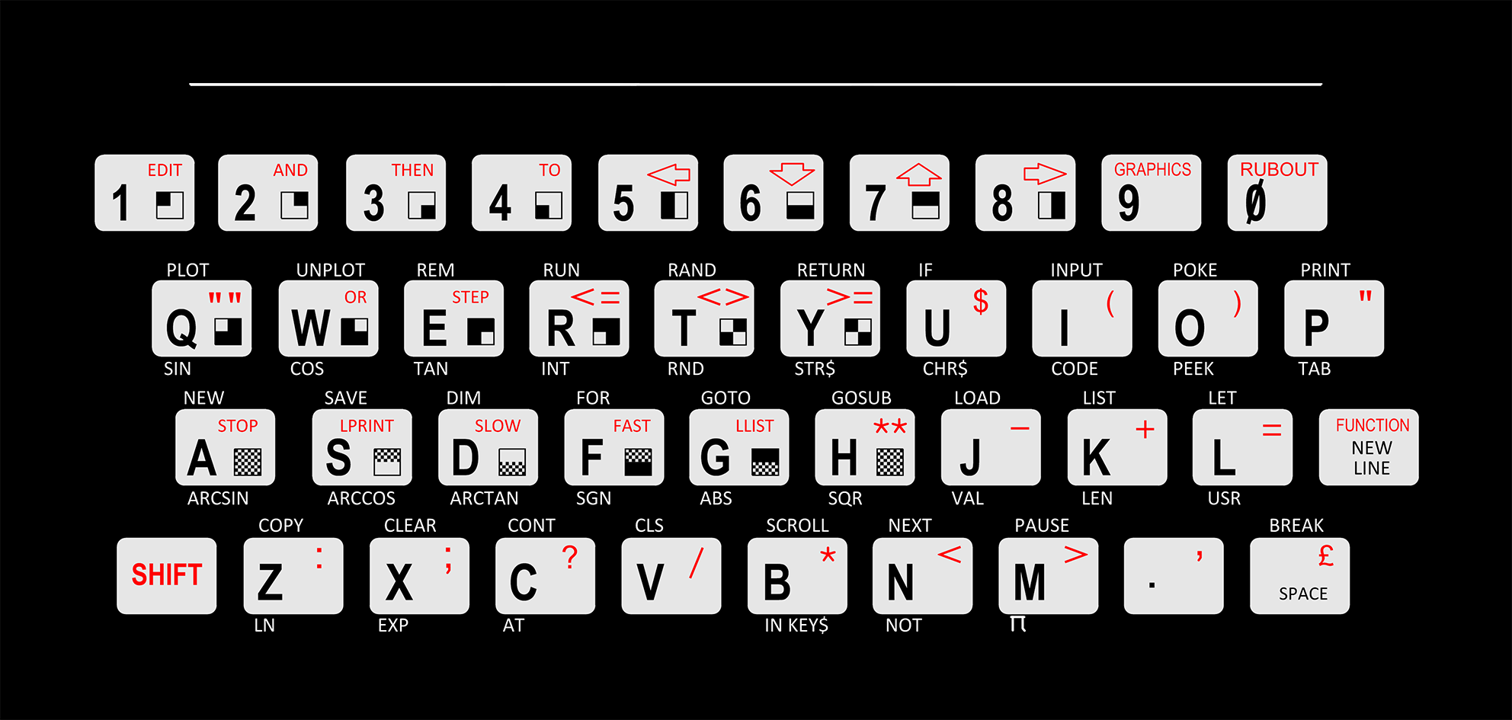
keyboard/keyboard_zx81_color.png
