abaffa/zx81/project/board_keyboard_zx80.png

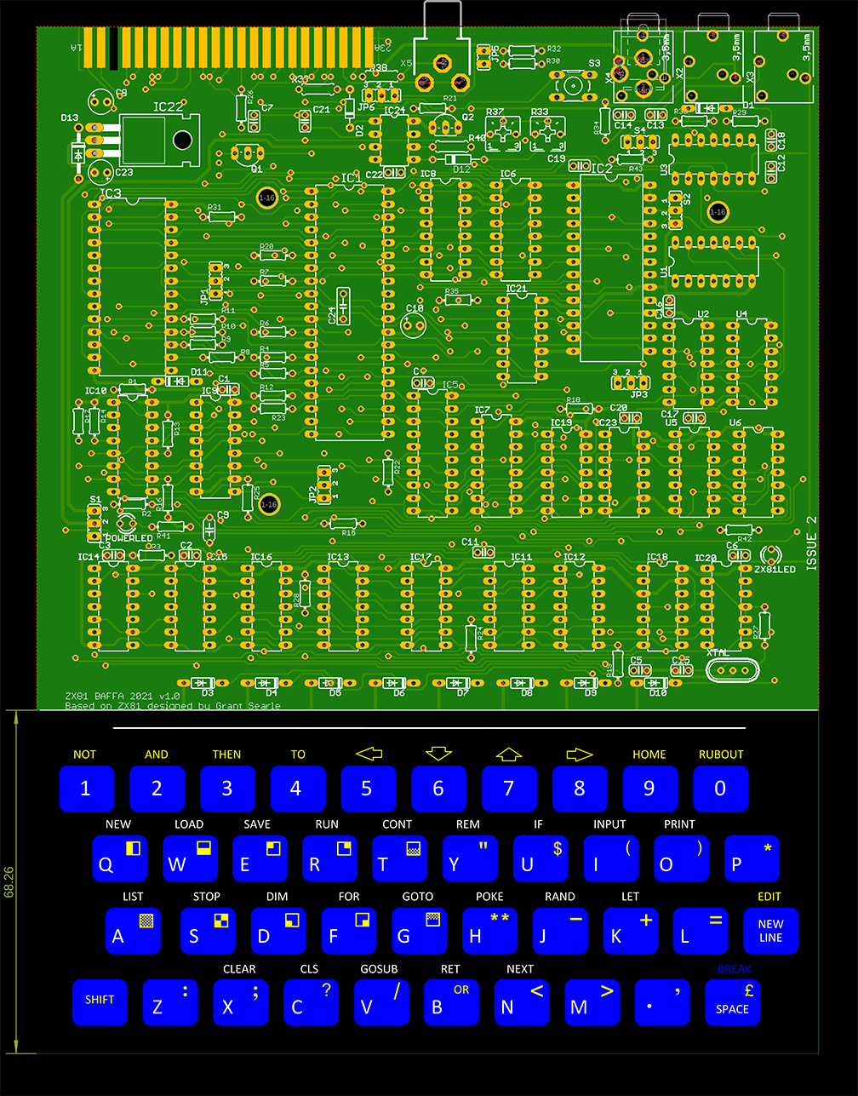
project/board_keyboard_zx80.png
