abaffa/zx81/project/board_keyboard_zx81.png

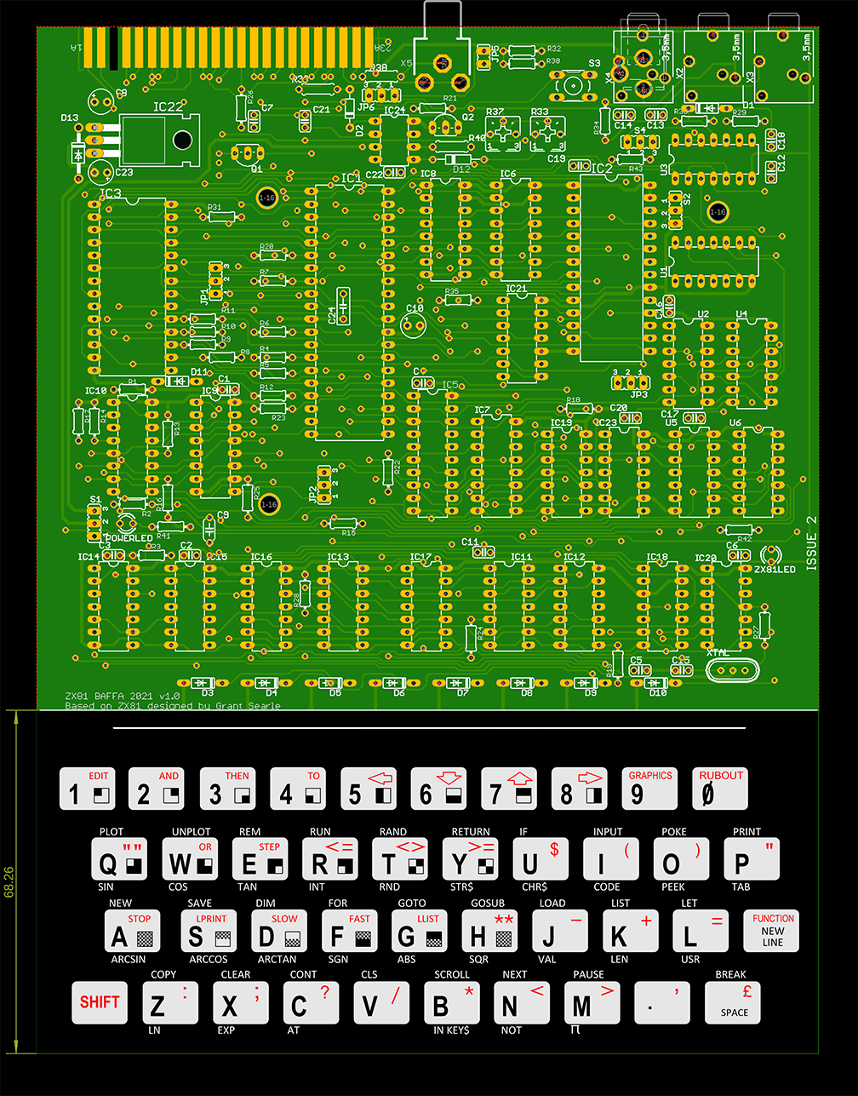
project/board_keyboard_zx81.png
