abaffa/zx81/stickers/_sample_applied_stickers.png

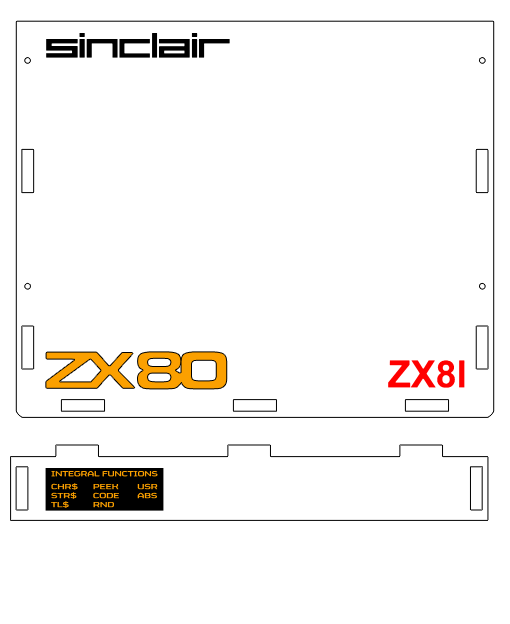
stickers/_sample_applied_stickers.png
