abaffa/zx81/stickers/sticker_Machine Labels_300dpi.png

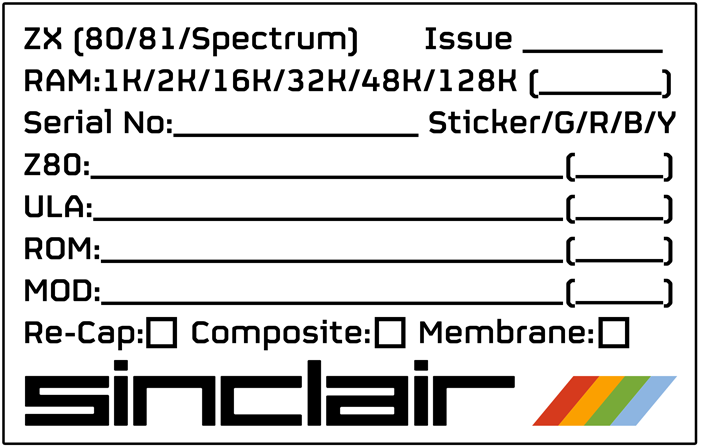
stickers/sticker_Machine Labels_300dpi.png
