abaffa/zx81/stickers/sticker_Machine Labels_x5_50.jpg

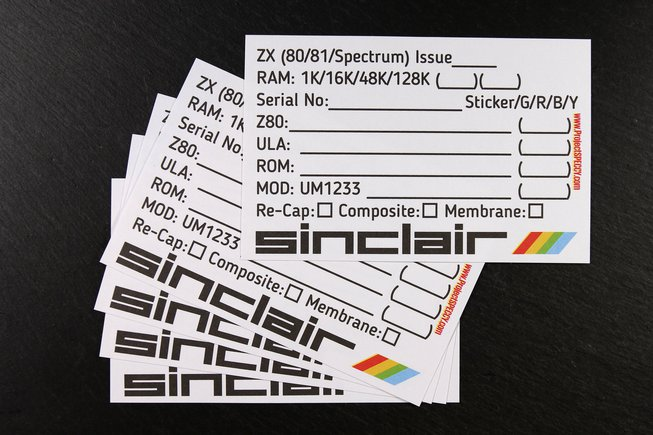
stickers/sticker_Machine Labels_x5_50.jpg
