abaffa/zx81/stickers/stickers_300dpi.png

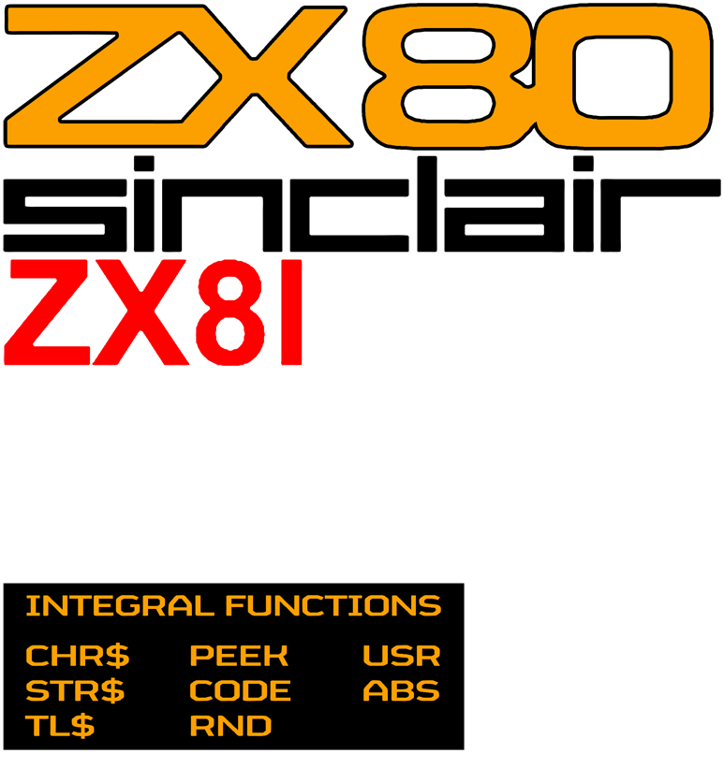
stickers/stickers_300dpi.png
