abaffa/zx81/Tabela Eproms Otimizada.jpg

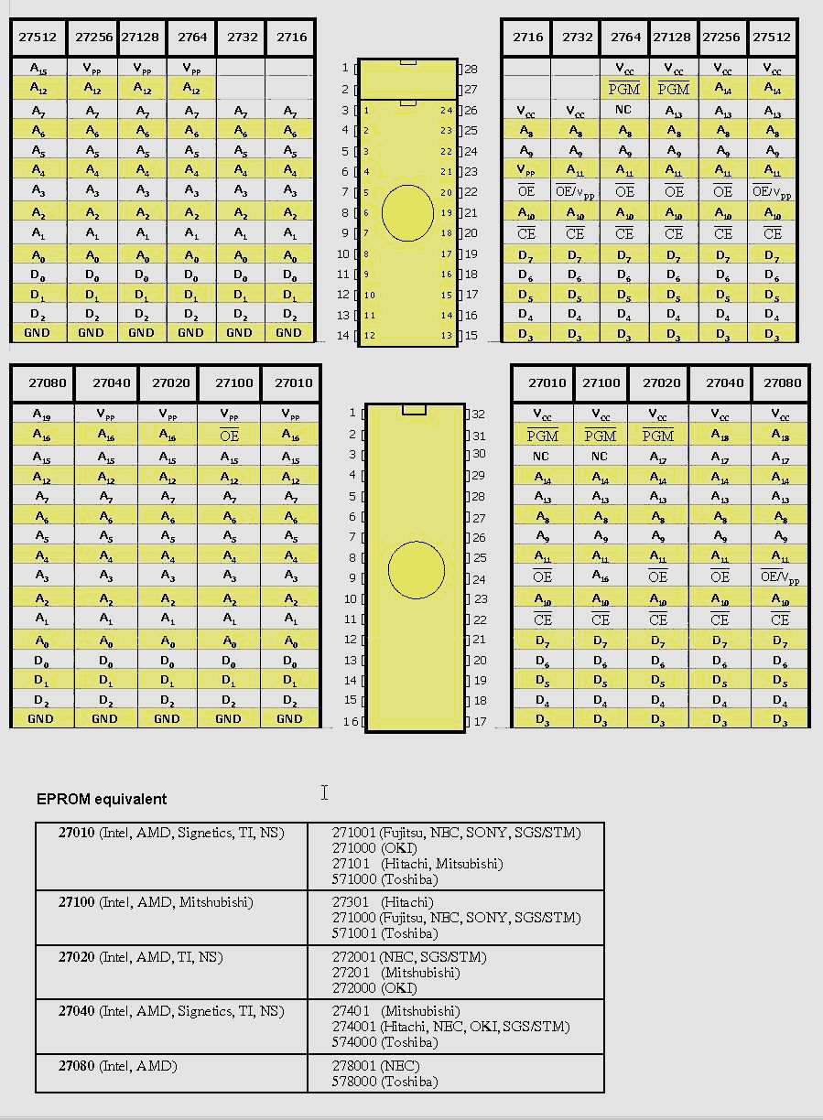
Tabela Eproms Otimizada.jpg
