abaffa/zx81/case_zx81/case1/files/zx81_case_top-vertical.stl

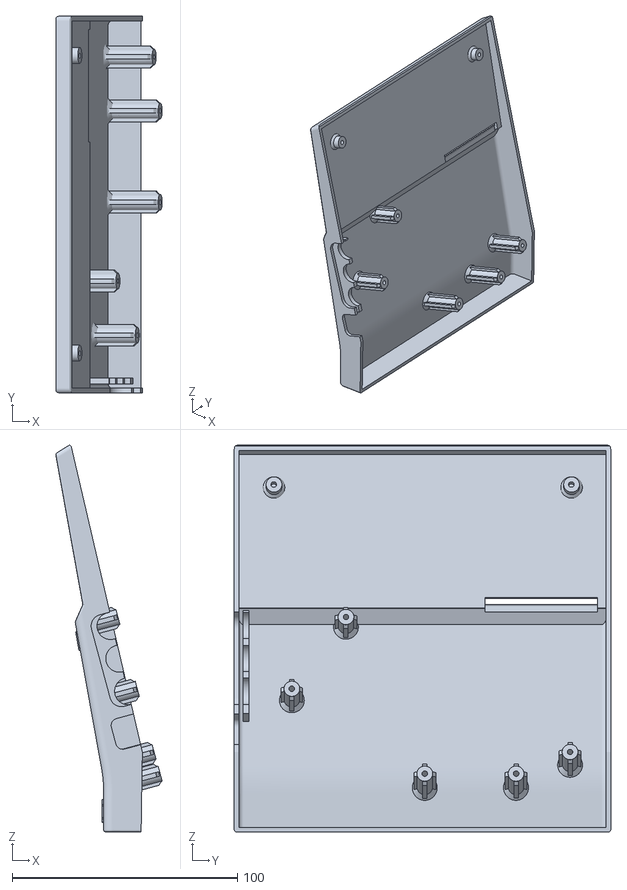
[picture p129: CAD file, 2022-02-01]
case_zx81/case1/files/zx81_case_top-vertical.stl
47.2 x 167.0 x 171.7
