abaffa/zx81/case_zx81/case3/files/zx81Bottom-EuroPort.stl

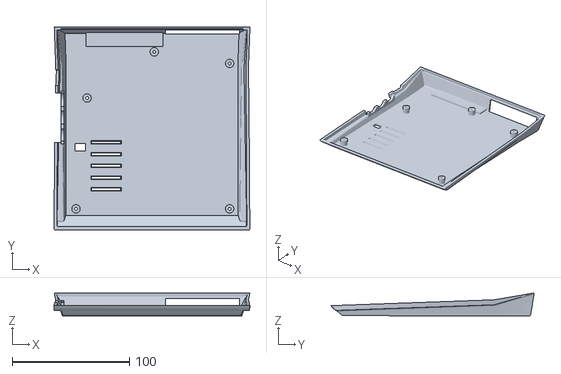
[picture p130: CAD file, 2022-02-01]
case_zx81/case3/files/zx81Bottom-EuroPort.stl
167.2 x 173.3 x 19.6
