abaffa/zx81/case_zxspectrum/files/Spectrum_case3.stl

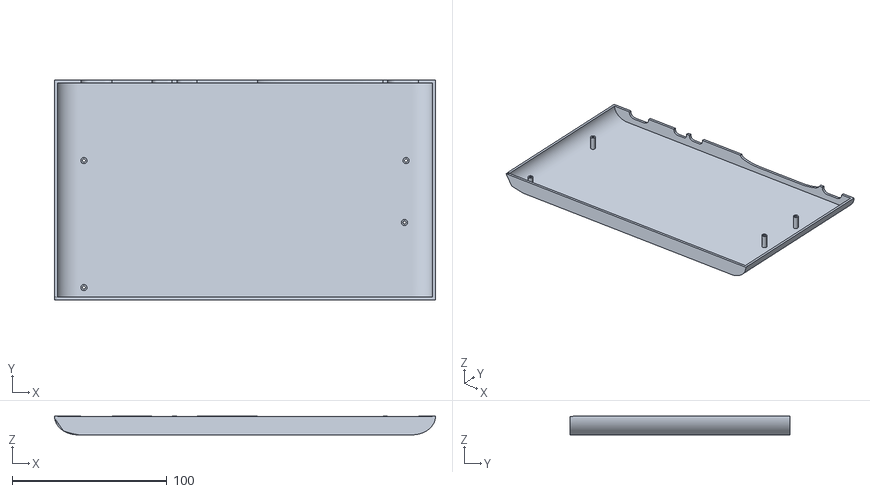
[picture p131: CAD file, 2022-02-01]
case_zxspectrum/files/Spectrum_case3.stl
246.0 x 142.0 x 12.1
