abaffa/zx81/case_zx80/case1/files/carcasa_v20.3t_no_av_hole.stl

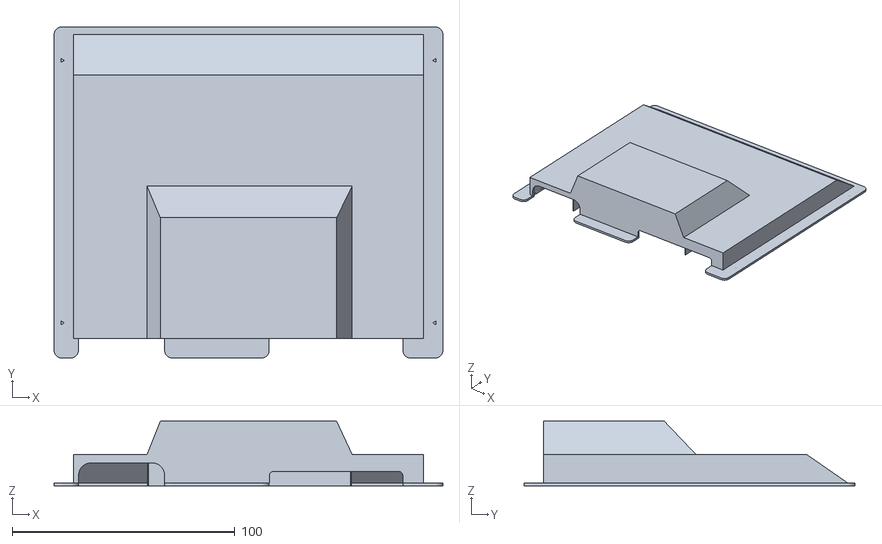
[picture p132: CAD file, 2022-01-24]
case_zx80/case1/files/carcasa_v20.3t_no_av_hole.stl
174.6 x 148.7 x 29.0
