abaffa/zx81/case_zx81/case1/files/zx81_case_bottom.stl

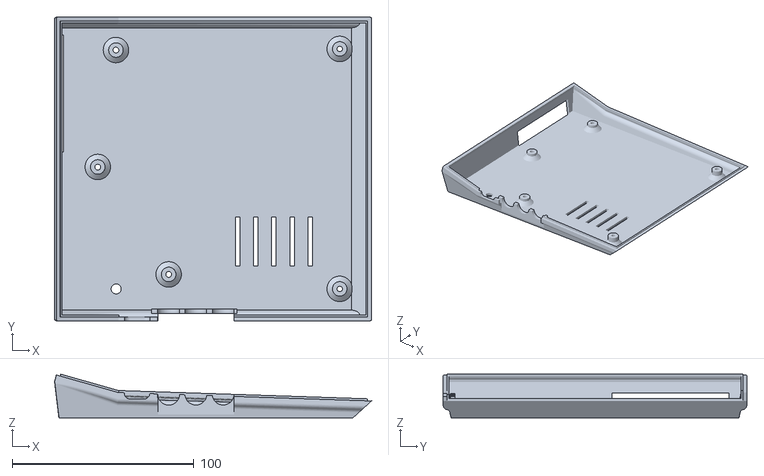
[picture p133: CAD file, 2022-02-01]
case_zx81/case1/files/zx81_case_bottom.stl
174.4 x 167.0 x 24.1
