abaffa/zx81/case_zx81/case3/files/zx81Bottom.stl

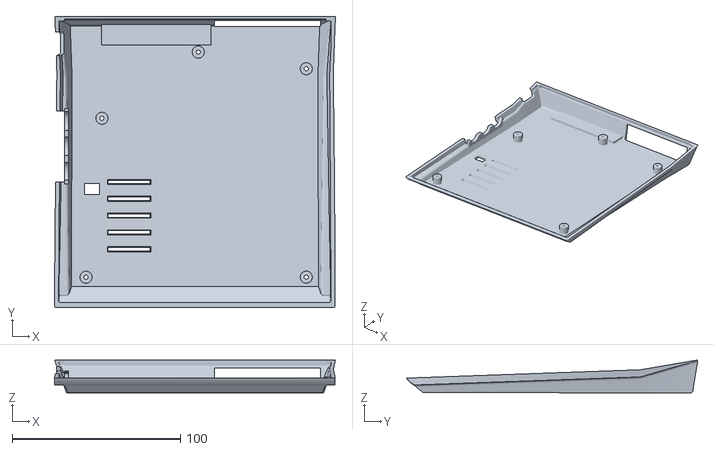
[picture p134: CAD file, 2022-02-01]
case_zx81/case3/files/zx81Bottom.stl
167.2 x 173.3 x 19.6
