abaffa/zx81/case_zx80/case1/files/carcasa_v14.1a.stl

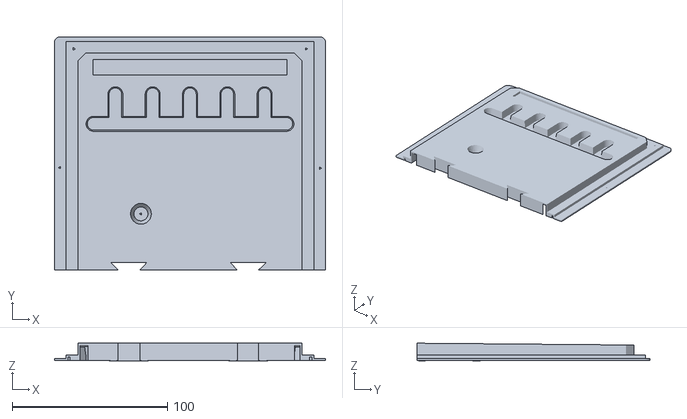
[picture p135: CAD file, 2022-01-24]
case_zx80/case1/files/carcasa_v14.1a.stl
174.3 x 150.1 x 11.3
