abaffa/zx81/case_zx80/case1/files/abajo_entero_switch_soportes.stl

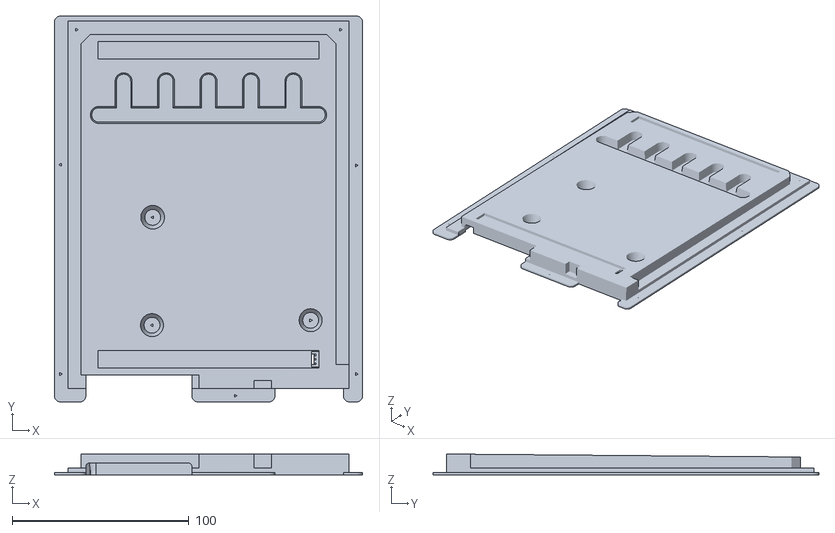
[picture p136: CAD file, 2022-01-24]
case_zx80/case1/files/abajo_entero_switch_soportes.stl
174.3 x 218.3 x 11.9
