abaffa/zx81/case_zx80/case1/files/abajo_b_switch_no_sup.stl

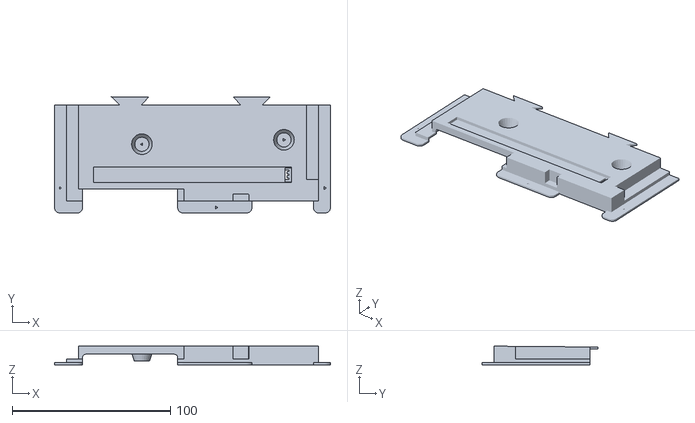
[picture p137: CAD file, 2022-01-24]
case_zx80/case1/files/abajo_b_switch_no_sup.stl
174.3 x 73.3 x 11.8
