abaffa/zx81/keyboard/keyboard_metal_domes.pdf

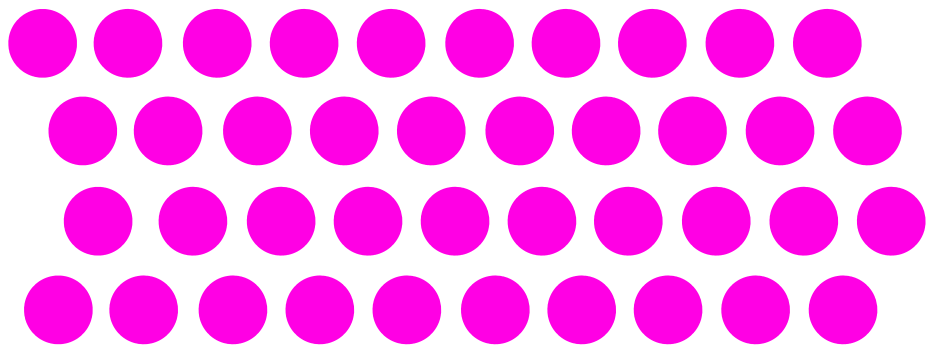
[picture p206: page 1]
