abaffa/zx81/keyboard/keyboard_polypropylene_mask.pdf

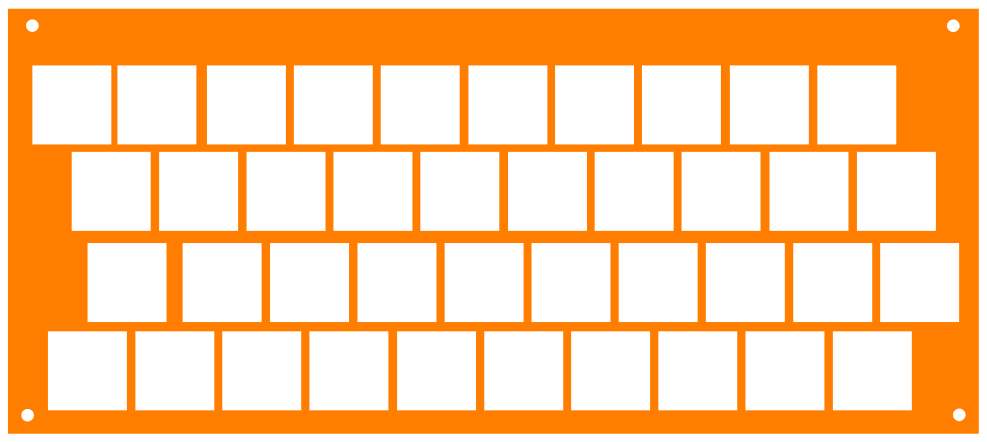
[picture p207: page 1]
