abaffa/zx81/project/board_bottom_circuit.pdf

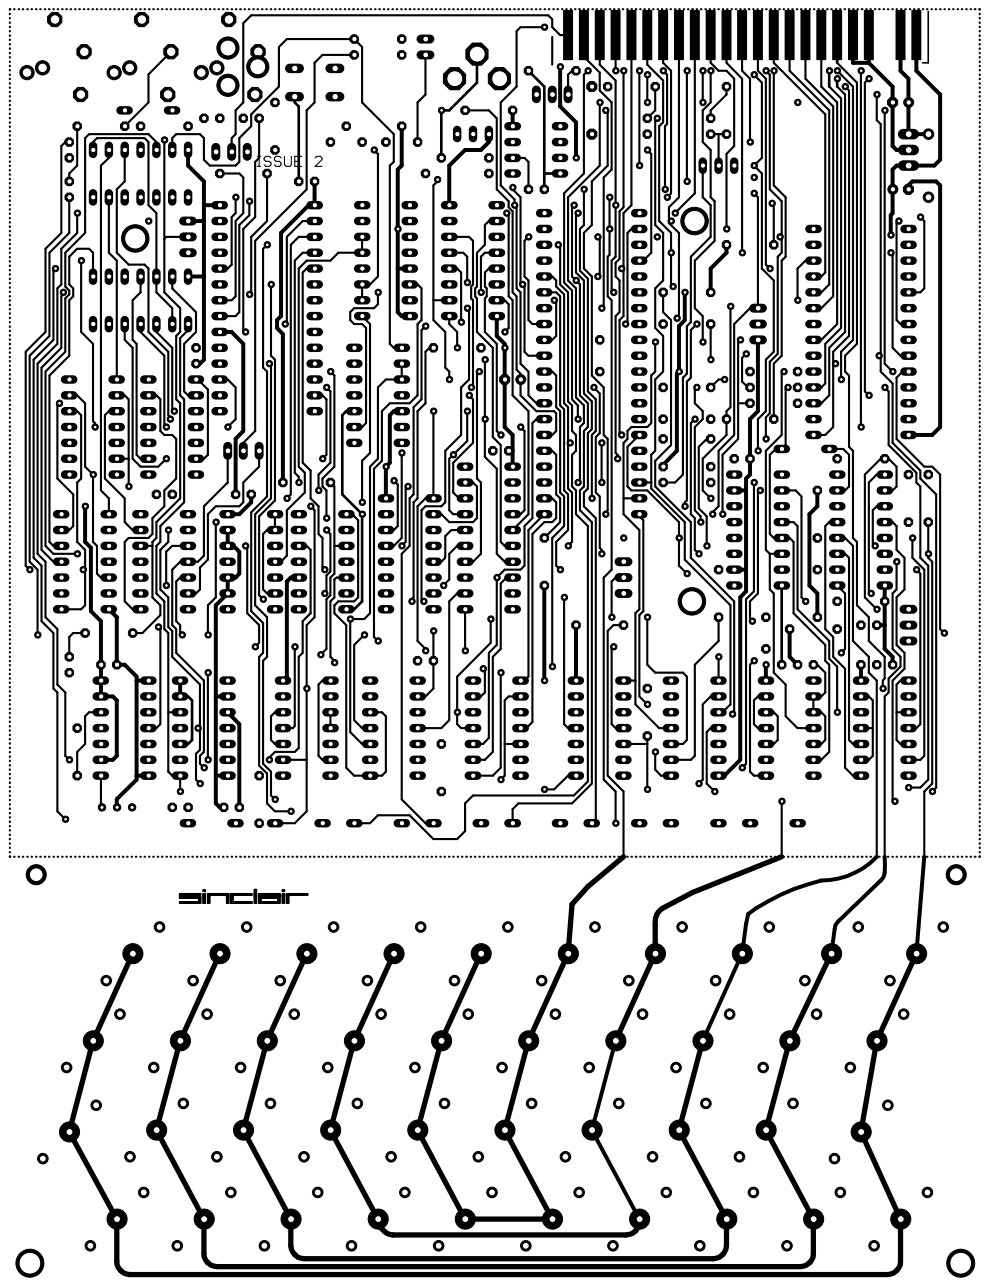
[picture p208: page 1]
