abaffa/zx81/project/board_top_circuit.pdf

IC1

IC2

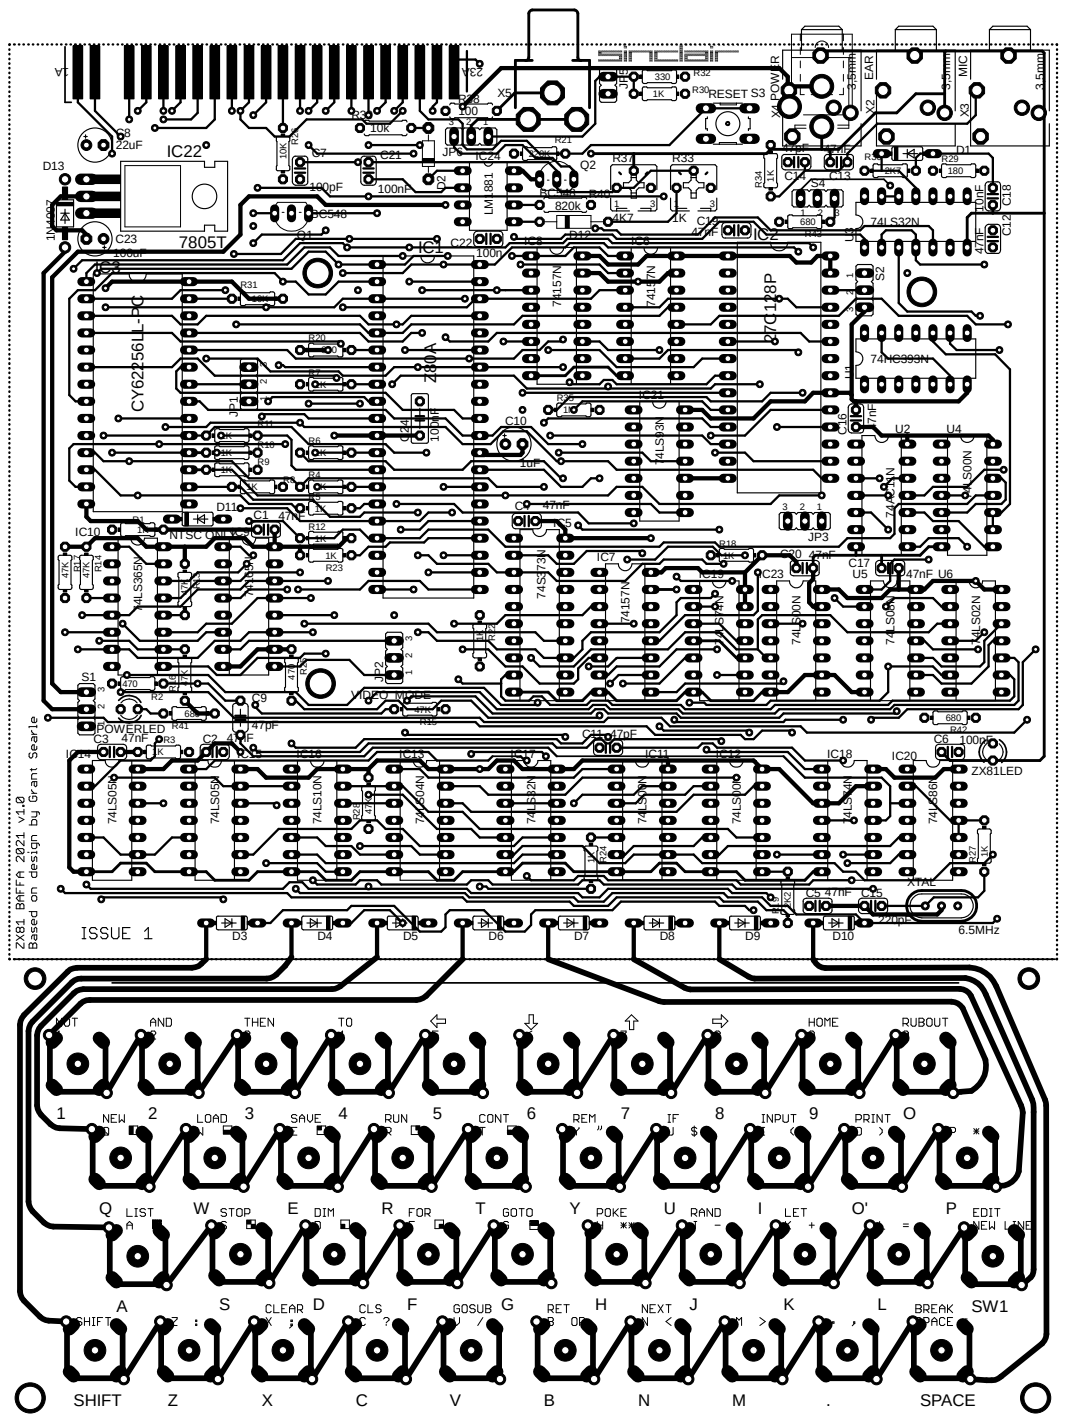
[picture p209: page 1]
