abaffa/zx81/_zx81/peripherals/ZX80_Edge_Connector_Diagram.pdf

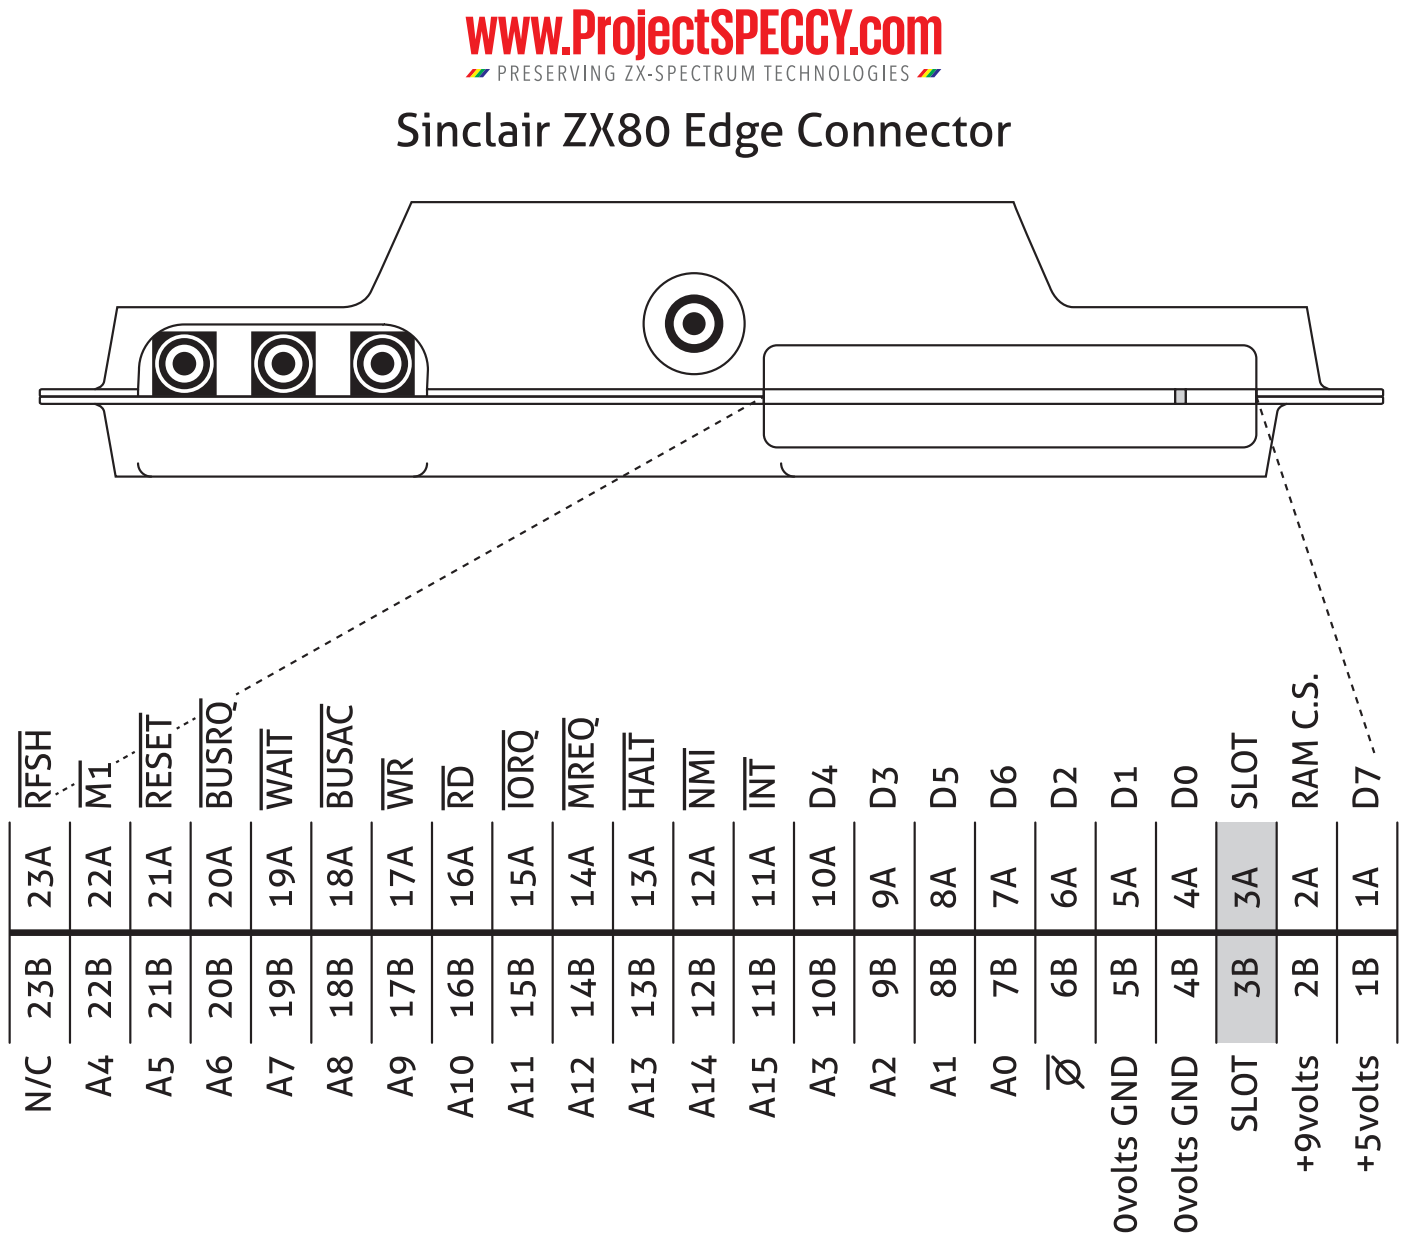
[picture p210: page 1]
