abaffa/zx81/_zx81/peripherals/ZX81_Edge_Connector_Diagram.pdf

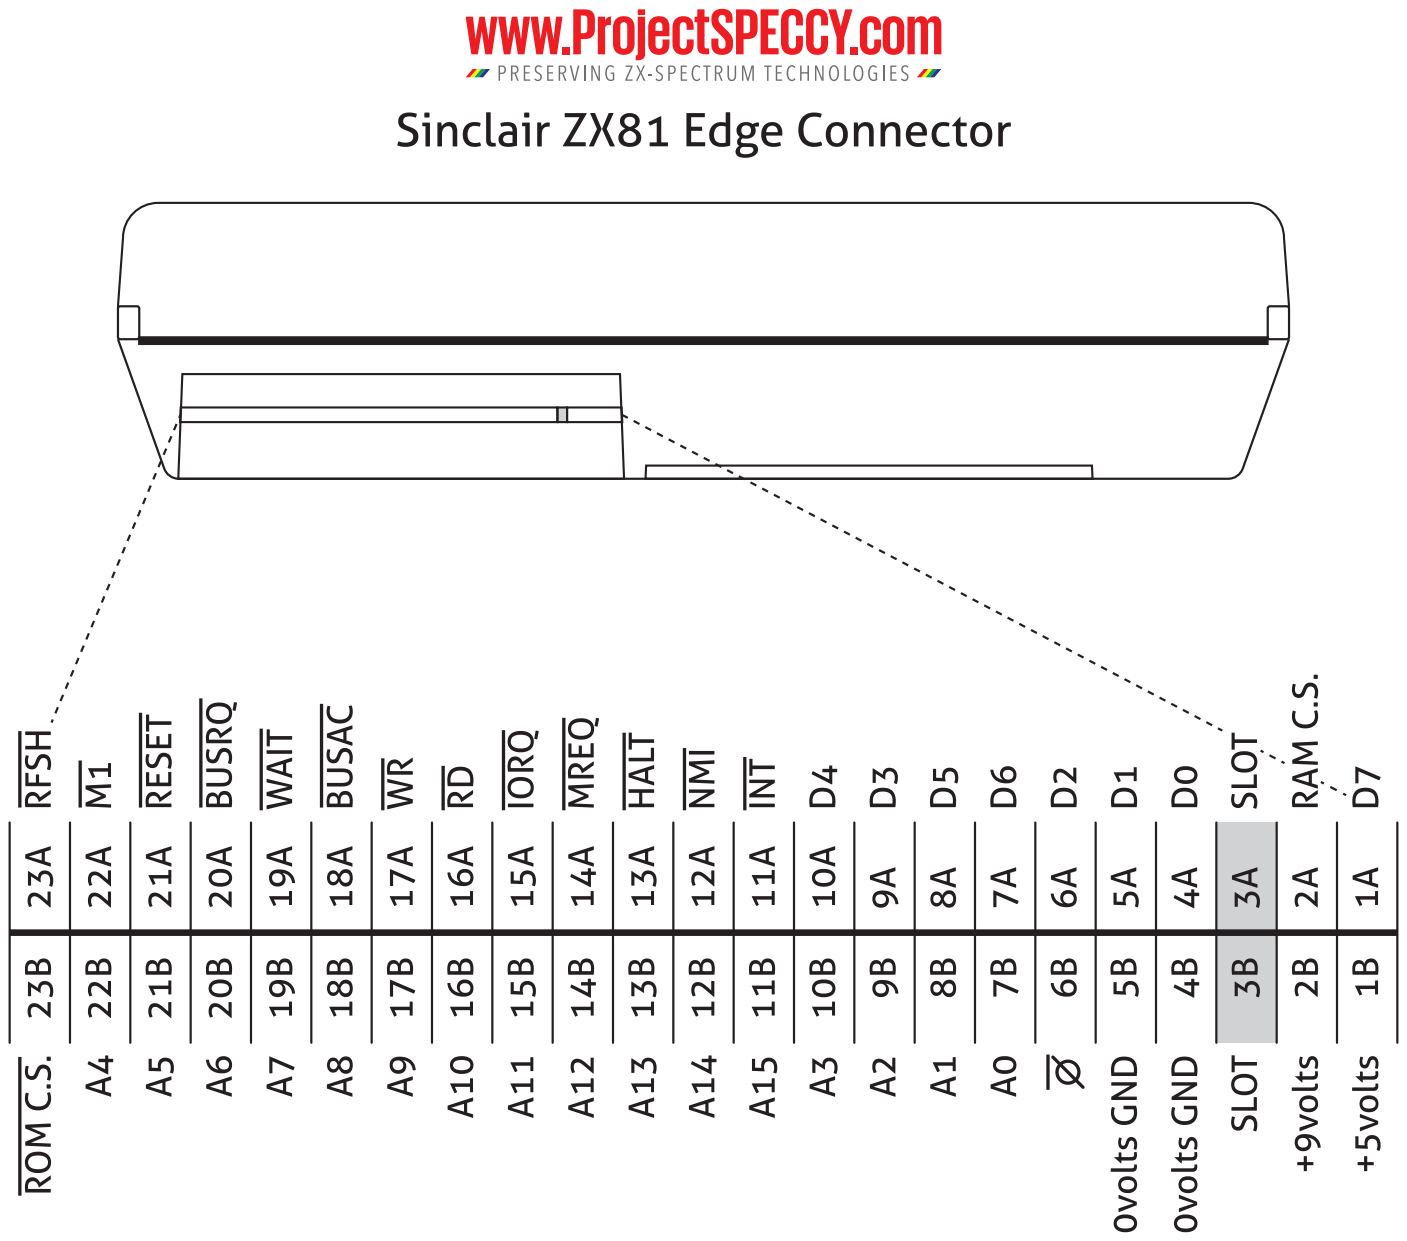
[picture p211: page 1]
